danwerner21/we816/Support/images/case8.jpg

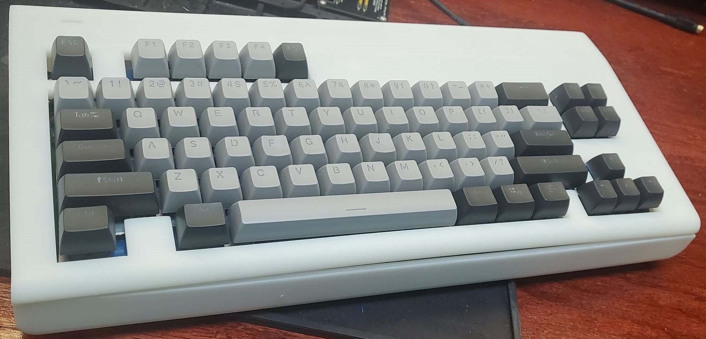
Support/images/case8.jpg
