danwerner21/we816/Support/images/case11.jpg

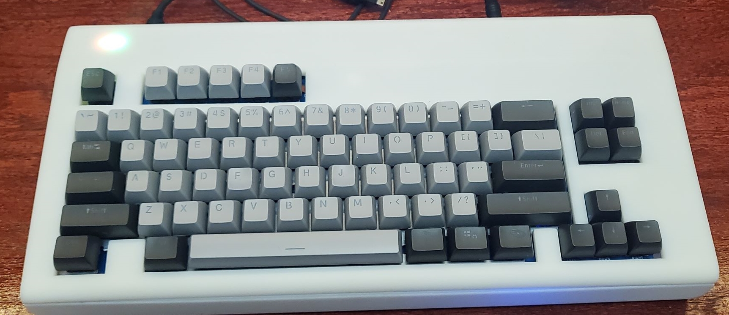
Support/images/case11.jpg
