danwerner21/we816/Support/images/case14.jpg

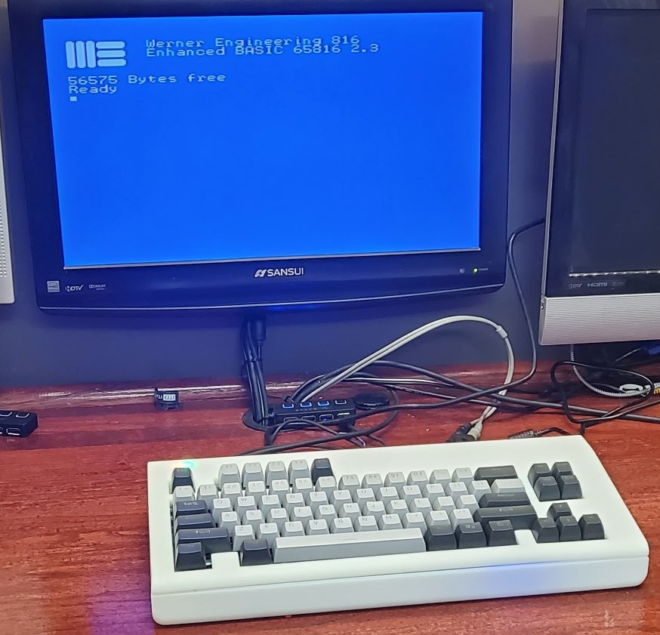
Support/images/case14.jpg
