danwerner21/we816/Support/images/case15.jpg

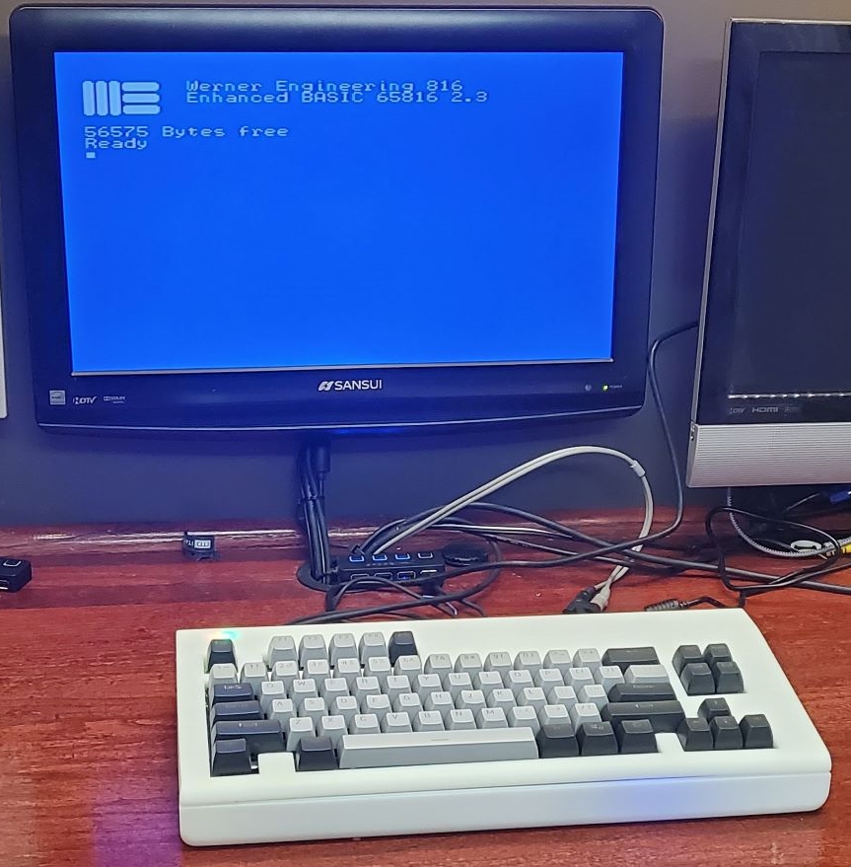
Support/images/case15.jpg
