danwerner21/we816/Hardware/file5FFCADA1.kicad_sch

## KiCad design Hardware/file5FFCADA1.kicad_sch (2022-08-01)

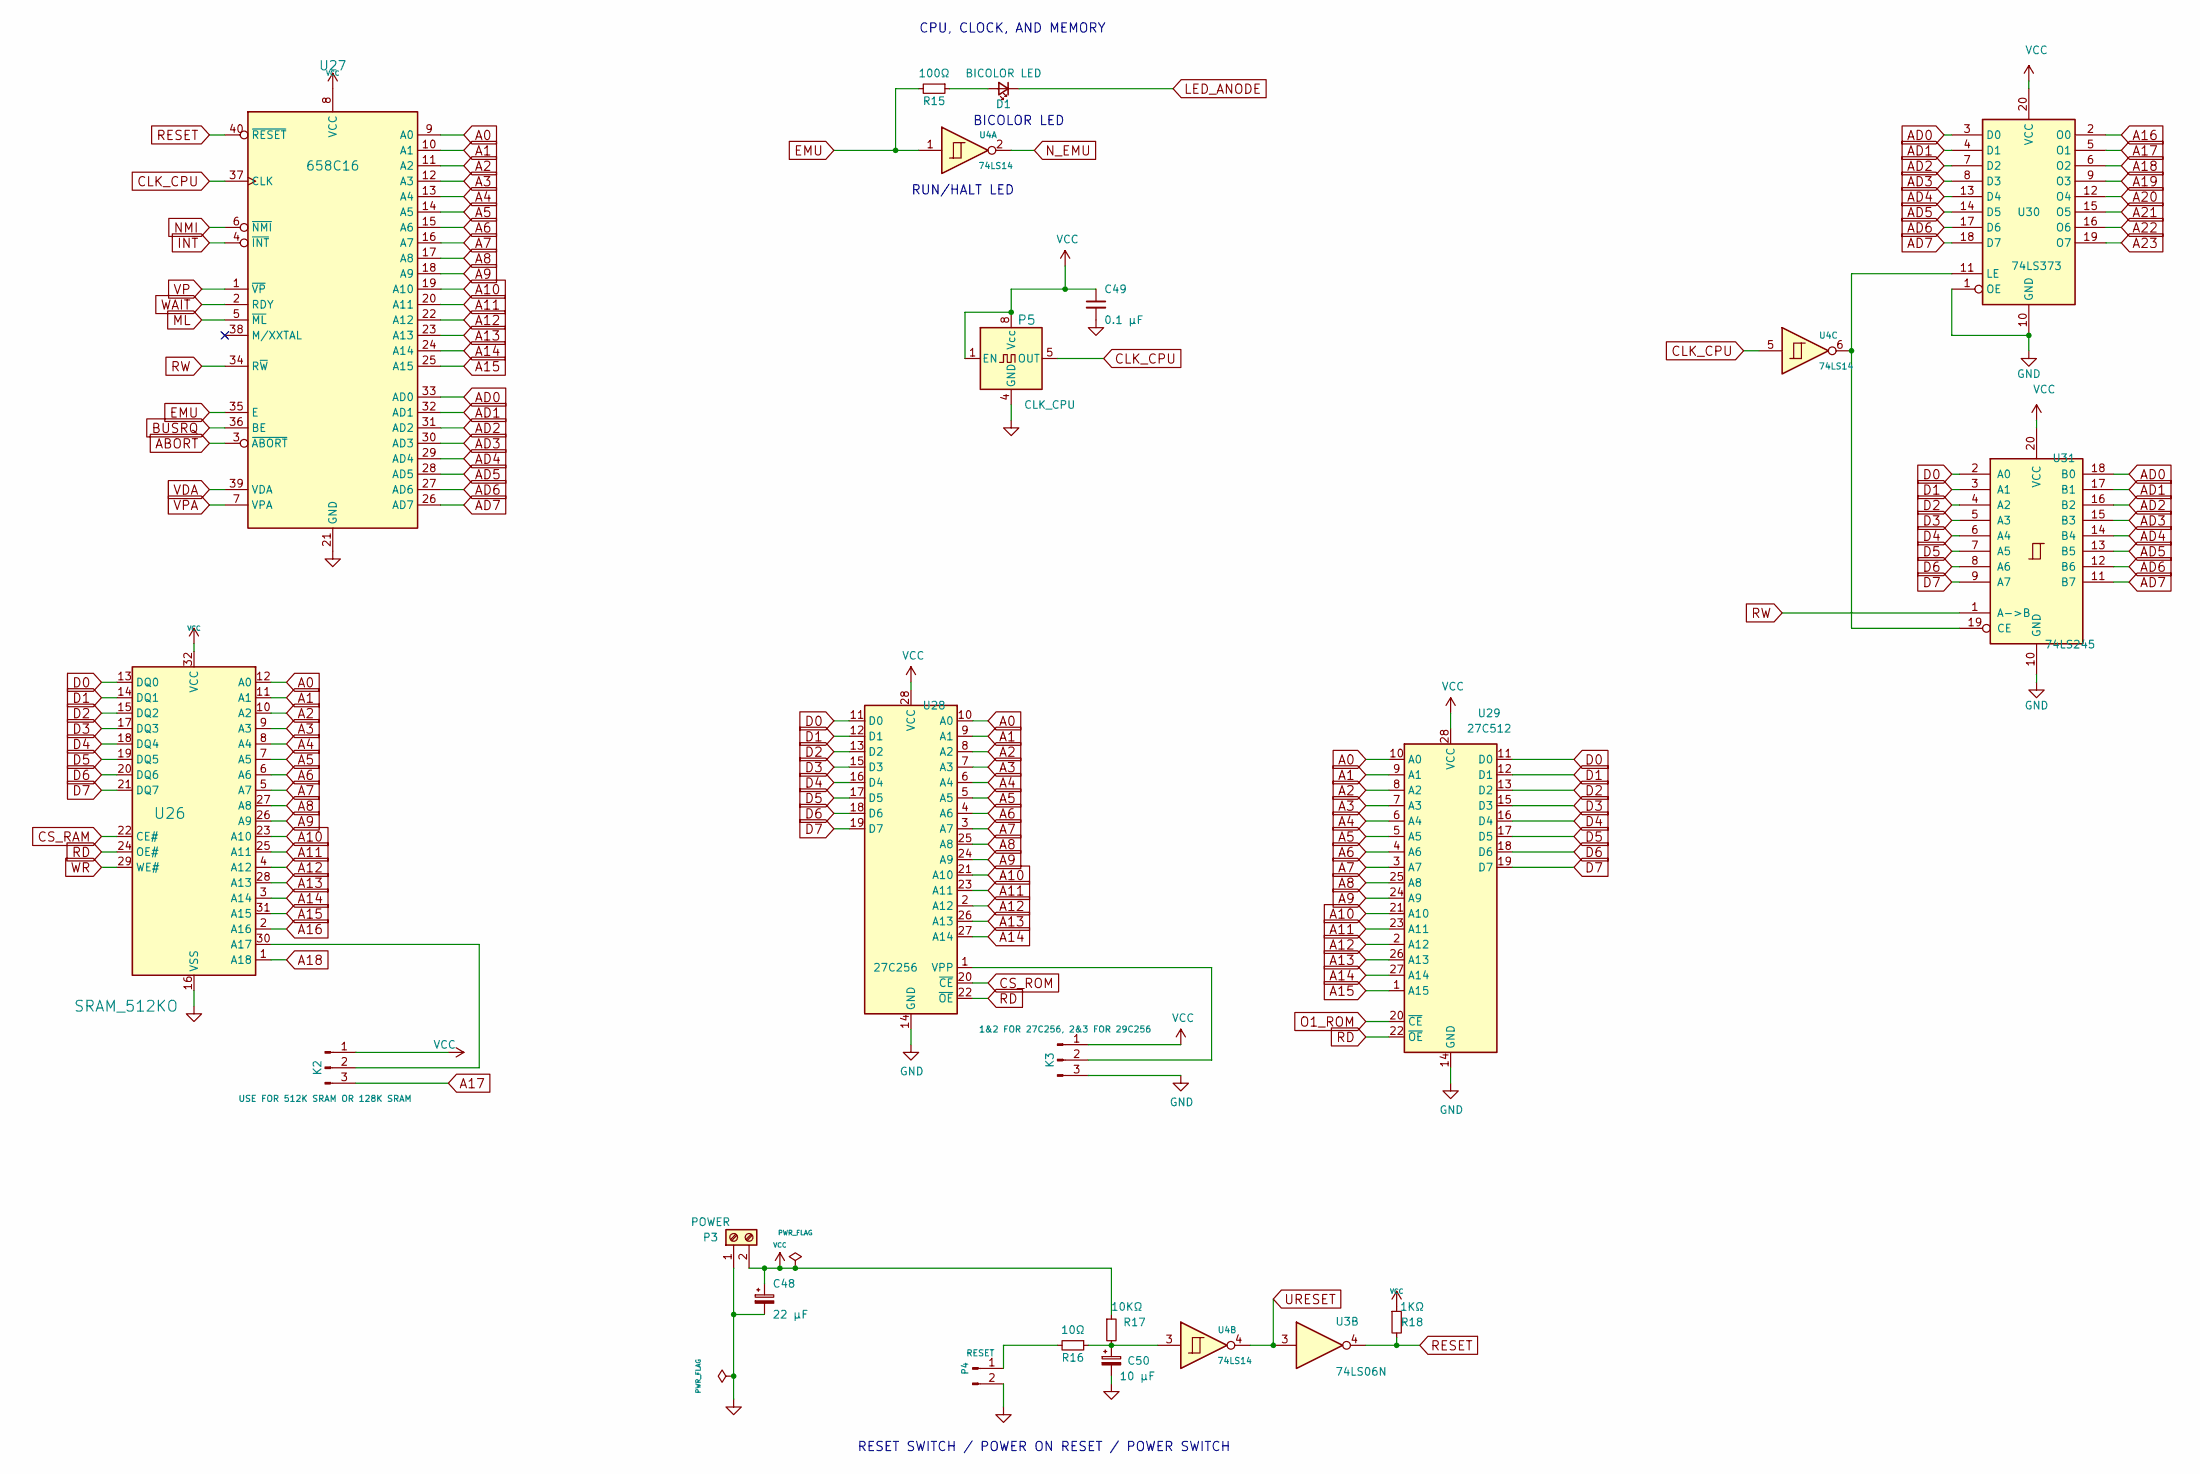
[picture p60: schematic file5FFCADA1.kicad_sch]

Parts:
C48: 22 µF; CP_Radial_D4.0mm_P2.00mm
C49: 0.1 µF; C_Rect_L7.0mm_W2.0mm_P5.00mm
C50: 10 µF; CP_Radial_D4.0mm_P2.00mm
D1: BICOLOR LED; LED_D5.0mm
K2: USE FOR 512K SRAM OR 128K SRAM; PinHeader_1x03_P2.54mm_Vertical
K3: 1&2 FOR 27C256, 2&3 FOR 29C256; PinHeader_1x03_P2.54mm_Vertical
P3: POWER; TerminalBlock_RND_205-00003_1x04_P5.00mm_Horizontal
P4: RESET; PinHeader_1x02_P2.54mm_Vertical
P5: CLK_CPU; Oscillator_DIP-8
R15: 100Ω; R_Axial_DIN0204_L3.6mm_D1.6mm_P5.08mm_Horizontal
R16: 10Ω; R_Axial_DIN0204_L3.6mm_D1.6mm_P5.08mm_Horizontal
R17: 10KΩ; R_Axial_DIN0204_L3.6mm_D1.6mm_P5.08mm_Horizontal
R18: 1KΩ; R_Axial_DIN0204_L3.6mm_D1.6mm_P5.08mm_Horizontal
U3: 74LS06N; DIP-14_W7.62mm_Socket
U4: 74LS14; DIP-14_W7.62mm_Socket_LongPads
U26: SRAM_512KO; DIP-32_W15.24mm
U27: 658C16; DIP-40_W15.24mm_Socket
U28: 27C256; DIP-28_W15.24mm
U29: 27C512; DIP-28_W15.24mm
U30: 74LS373; DIP-20_W7.62mm_Socket_LongPads
U31: 74LS245; DIP-20_W7.62mm_Socket_LongPads

Connections:
A0: U26.12 (A0), U27.9 (A0), U28.10 (A0), U29.10 (A0)
A1: U26.11 (A1), U27.10 (A1), U28.9 (A1), U29.9 (A1)
A2: U26.10 (A2), U27.11 (A2), U28.8 (A2), U29.8 (A2)
A3: U26.9 (A3), U27.12 (A3), U28.7 (A3), U29.7 (A3)
A4: U26.8 (A4), U27.13 (A4), U28.6 (A4), U29.6 (A4)
A5: U26.7 (A5), U27.14 (A5), U28.5 (A5), U29.5 (A5)
A6: U26.6 (A6), U27.15 (A6), U28.4 (A6), U29.4 (A6)
A7: U26.5 (A7), U27.16 (A7), U28.3 (A7), U29.3 (A7)
A8: U26.27 (A8), U27.17 (A8), U28.25 (A8), U29.25 (A8)
A9: U26.26 (A9), U27.18 (A9), U28.24 (A9), U29.24 (A9)
A10: U26.23 (A10), U27.19 (A10), U28.21 (A10), U29.21 (A10)
A11: U26.25 (A11), U27.20 (A11), U28.23 (A11), U29.23 (A11)
A12: U26.4 (A12), U27.22 (A12), U28.2 (A12), U29.2 (A12)
A13: U26.28 (A13), U27.23 (A13), U28.26 (A13), U29.26 (A13)
A14: U26.3 (A14), U27.24 (A14), U28.27 (A14), U29.27 (A14)
A15: U26.31 (A15), U27.25 (A15), U29.1 (A15)
A16: U26.2 (A16), U30.2 (O0)
A17: K2.3, U30.5 (O1)
A18: U26.1 (A18), U30.6 (O2)
A19: U30.9 (O3)
A20: U30.12 (O4)
A21: U30.15 (O5)
A22: U30.16 (O6)
A23: U30.19 (O7)
ABORT: U27.3 (~ABORT)
AD0: U27.33 (AD0), U30.3 (D0), U31.18 (B0)
AD1: U27.32 (AD1), U30.4 (D1), U31.17 (B1)
AD2: U27.31 (AD2), U30.7 (D2), U31.16 (B2)
AD3: U27.30 (AD3), U30.8 (D3), U31.15 (B3)
AD4: U27.29 (AD4), U30.13 (D4), U31.14 (B4)
AD5: U27.28 (AD5), U30.14 (D5), U31.13 (B5)
AD6: U27.27 (AD6), U30.17 (D6), U31.12 (B6)
AD7: U27.26 (AD7), U30.18 (D7), U31.11 (B7)
BUSRQ: U27.36 (BE)
CLK_CPU: P5.5 (OUT), U4.5, U27.37 (CLK)
CS_RAM: U26.22 (CE#)
CS_ROM: U28.20 (~CE)
D0: U26.13 (DQ0), U28.11 (D0), U29.11 (D0), U31.2 (A0)
D1: U26.14 (DQ1), U28.12 (D1), U29.12 (D1), U31.3 (A1)
D2: U26.15 (DQ2), U28.13 (D2), U29.13 (D2), U31.4 (A2)
D3: U26.17 (DQ3), U28.15 (D3), U29.15 (D3), U31.5 (A3)
D4: U26.18 (DQ4), U28.16 (D4), U29.16 (D4), U31.6 (A4)
D5: U26.19 (DQ5), U28.17 (D5), U29.17 (D5), U31.7 (A5)
D6: U26.20 (DQ6), U28.18 (D6), U29.18 (D6), U31.8 (A6)
D7: U26.21 (DQ7), U28.19 (D7), U29.19 (D7), U31.9 (A7)
EMU: R15.2, U4.1, U27.35 (E)
GND: C48.2, C49.2, C50.2, K3.3, P3.1, P4.2, P5.4 (GND), U26.16 (VSS), U27.21 (GND), U28.14 (GND), U29.14 (GND), U30.1 (OE), U30.10 (GND), U31.10 (GND)
INT: U27.4 (~INT)
LED_ANODE: D1.1 (K)
ML: U27.5 (~ML)
NMI: U27.6 (~NMI)
N_EMU: U4.2
unnamed: C50.1, R16.1, R17.2, U4.3
unnamed: D1.2 (A), R15.1
unnamed: K2.2, U26.30 (A17)
unnamed: K3.2, U28.1 (VPP)
unnamed: P4.1, R16.2
unnamed: U4.6, U30.11 (LE), U31.19 (CE)
O1_ROM: U29.20 (~CE)
RD: U26.24 (OE#), U28.22 (~OE), U29.22 (~OE)
RESET: R18.2, U3.4, U27.40 (~RESET)
RW: U27.34 (R~W), U31.1 (A->B)
URESET: U3.3, U4.4
VCC: C48.1, C49.1, K2.1, K3.1, P3.2, P5.1 (EN), P5.8 (Vcc), R17.1, R18.1, U26.32 (VCC), U27.8 (VCC), U28.28 (VCC), U29.28 (VCC), U30.20 (VCC), U31.20 (VCC)
VDA: U27.39 (VDA)
VP: U27.1 (~VP)
VPA: U27.7 (VPA)
WAIT: U27.2 (RDY)
WR: U26.29 (WE#)

Notes on the sheet:
RUN/HALT LED
CPU, CLOCK, AND MEMORY
RESET SWITCH / POWER ON RESET / POWER SWITCH
BICOLOR LED
