danwerner21/we816/Hardware/file5FFCBF10.kicad_sch

## KiCad design Hardware/file5FFCBF10.kicad_sch (2022-08-01)

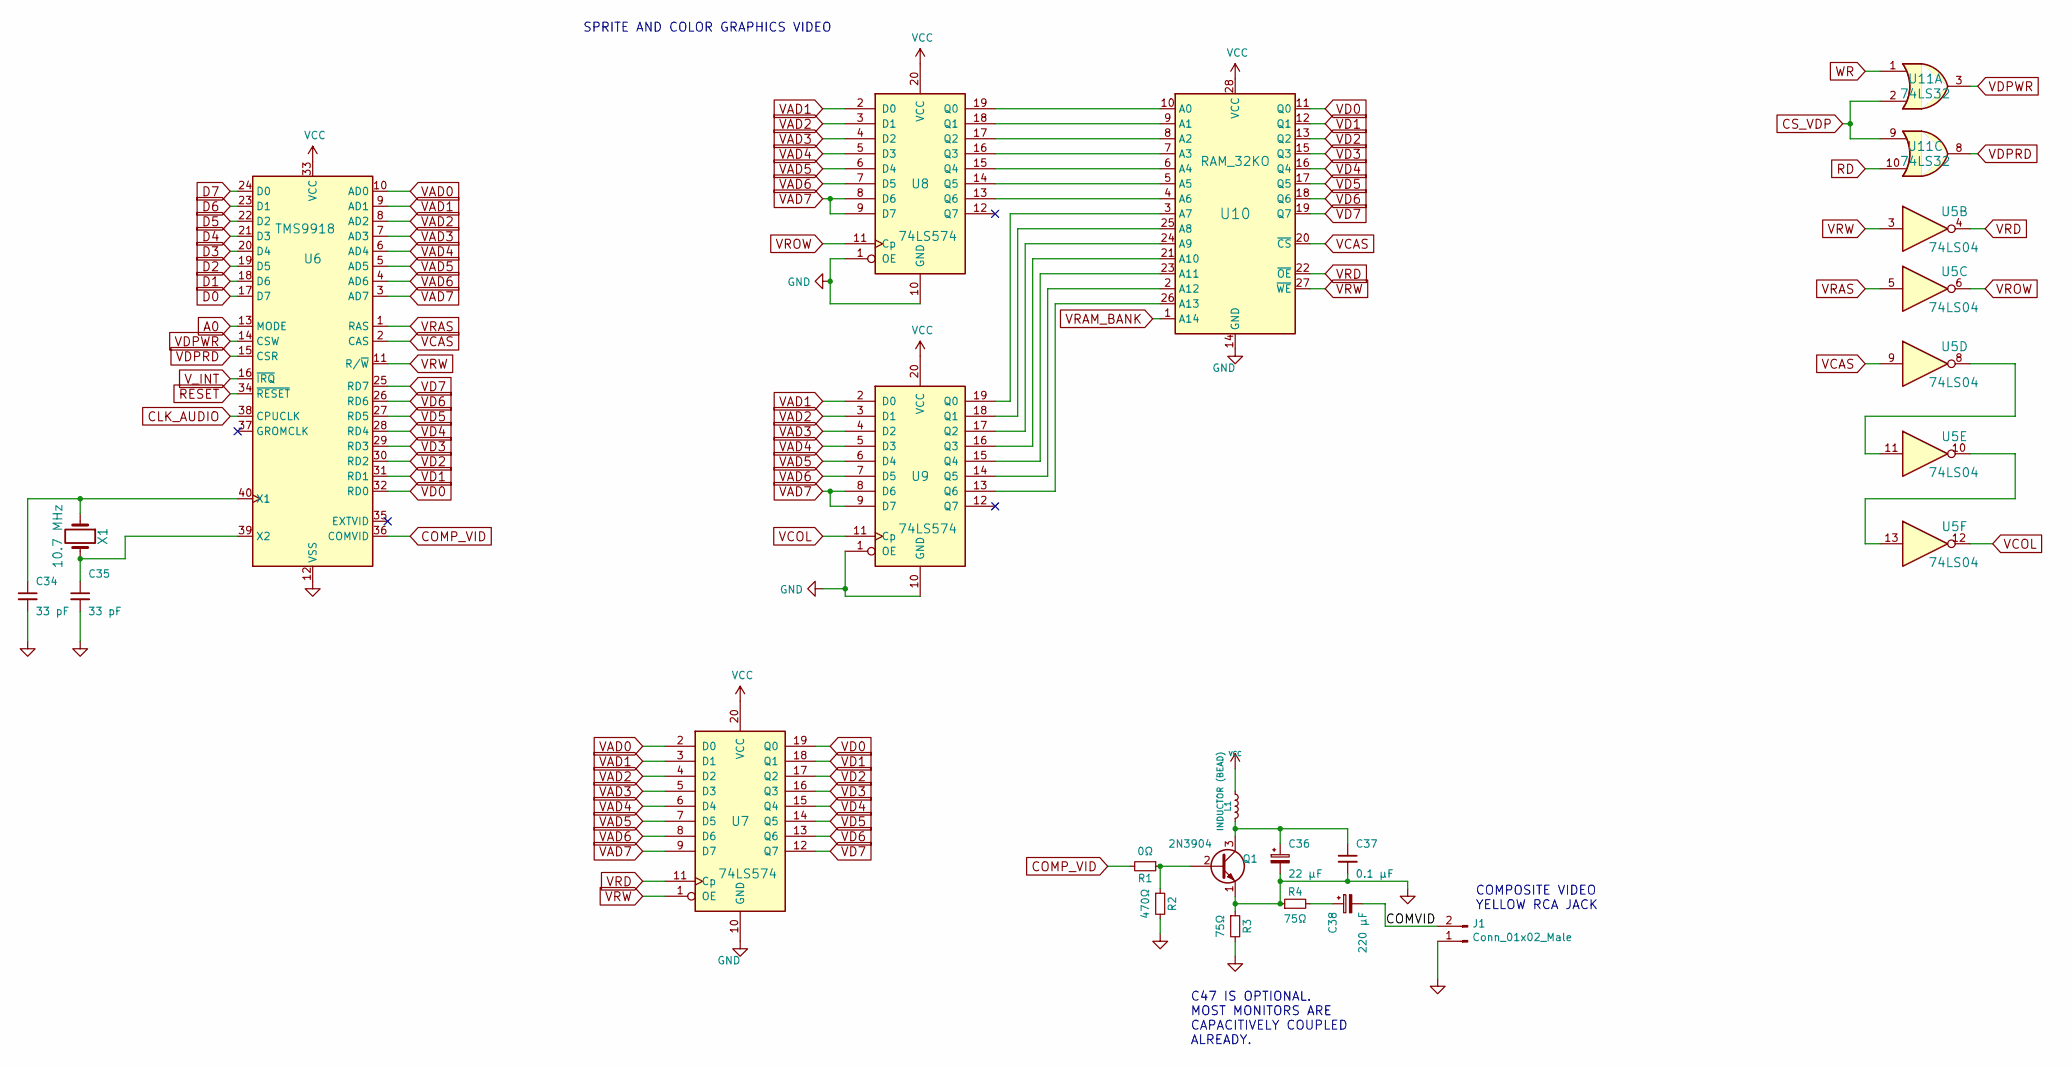
[picture p61: schematic file5FFCBF10.kicad_sch]

Parts:
C34, C35: 33 pF; C_Rect_L7.0mm_W2.0mm_P5.00mm
C36: 22 µF; CP_Radial_D4.0mm_P2.00mm
C37: 0.1 µF; C_Rect_L7.0mm_W2.0mm_P5.00mm
C38: 220 µF; CP_Radial_D4.0mm_P2.00mm
J1: Conn_01x02_Male; CUI_RCJ-041
L1: INDUCTOR (BEAD); R_Axial_DIN0207_L6.3mm_D2.5mm_P10.16mm_Horizontal
Q1: 2N3904; TO-92L_HandSolder
R1: 0Ω; R_Axial_DIN0204_L3.6mm_D1.6mm_P5.08mm_Horizontal
R2: 470Ω; R_Axial_DIN0204_L3.6mm_D1.6mm_P5.08mm_Horizontal
R3, R4: 75Ω; R_Axial_DIN0204_L3.6mm_D1.6mm_P5.08mm_Horizontal
U5: 74LS04; DIP-14_W7.62mm_Socket
U6: TMS9918; DIP-40_W15.24mm_Socket_LongPads
U7: 74LS574; DIP-20_W7.62mm_Socket
U8, U9: 74LS574; DIP-20_W7.62mm_Socket_LongPads
U10: RAM_32KO; DIP-28_W15.24mm
U11: 74LS32; DIP-14_W7.62mm_Socket
X1: 10.7 MHz; Crystal_HC18-U_Vertical

Connections:
A0: U6.13 (MODE)
CLK_AUDIO: U6.38 (CPUCLK)
COMP_VID: R1.2, U6.36 (COMVID)
COMVID: C38.2, J1.2
CS_VDP: U11.2, U11.9
D0: U6.17 (D7)
D1: U6.18 (D6)
D2: U6.19 (D5)
D3: U6.20 (D4)
D4: U6.21 (D3)
D5: U6.22 (D2)
D6: U6.23 (D1)
D7: U6.24 (D0)
GND: C34.2, C35.2, C36.2, C37.2, J1.1, Q1.1 (E), R2.2, R3.1, R3.2, R4.1, U6.12 (VSS), U7.10 (GND), U8.1 (OE), U8.10 (GND), U9.1 (OE), U9.10 (GND), U10.14 (GND)
unnamed: C34.1, U6.40 (X1), X1.1
unnamed: C35.1, U6.39 (X2), X1.2
unnamed: C36.1, C37.1, L1.2, Q1.3 (C)
unnamed: C38.1, R4.2
unnamed: Q1.2 (B), R1.1, R2.1
unnamed: U5.10, U5.13
unnamed: U5.8, U5.11
unnamed: U9.14 (Q5), U10.2 (A12)
unnamed: U9.19 (Q0), U10.3 (A7)
unnamed: U8.13 (Q6), U10.4 (A6)
unnamed: U8.14 (Q5), U10.5 (A5)
unnamed: U8.15 (Q4), U10.6 (A4)
unnamed: U8.16 (Q3), U10.7 (A3)
unnamed: U8.17 (Q2), U10.8 (A2)
unnamed: U8.18 (Q1), U10.9 (A1)
unnamed: U8.19 (Q0), U10.10 (A0)
unnamed: U9.16 (Q3), U10.21 (A10)
unnamed: U9.15 (Q4), U10.23 (A11)
unnamed: U9.17 (Q2), U10.24 (A9)
unnamed: U9.18 (Q1), U10.25 (A8)
unnamed: U9.13 (Q6), U10.26 (A13)
RD: U11.10
RESET: U6.34 (~RESET)
VAD0: U6.10 (AD0), U7.2 (D0)
VAD1: U6.9 (AD1), U7.3 (D1), U8.2 (D0), U9.2 (D0)
VAD2: U6.8 (AD2), U7.4 (D2), U8.3 (D1), U9.3 (D1)
VAD3: U6.7 (AD3), U7.5 (D3), U8.4 (D2), U9.4 (D2)
VAD4: U6.6 (AD4), U7.6 (D4), U8.5 (D3), U9.5 (D3)
VAD5: U6.5 (AD5), U7.7 (D5), U8.6 (D4), U9.6 (D4)
VAD6: U6.4 (AD6), U7.8 (D6), U8.7 (D5), U9.7 (D5)
VAD7: U6.3 (AD7), U7.9 (D7), U8.8 (D6), U8.9 (D7), U9.8 (D6), U9.9 (D7)
VCAS: U5.9, U6.2 (CAS), U10.20 (~CS)
VCC: L1.1, U6.33 (VCC), U7.20 (VCC), U8.20 (VCC), U9.20 (VCC), U10.28 (VCC)
VCOL: U5.12, U9.11 (Cp)
VD0: U6.32 (RD0), U7.19 (Q0), U10.11 (Q0)
VD1: U6.31 (RD1), U7.18 (Q1), U10.12 (Q1)
VD2: U6.30 (RD2), U7.17 (Q2), U10.13 (Q2)
VD3: U6.29 (RD3), U7.16 (Q3), U10.15 (Q3)
VD4: U6.28 (RD4), U7.15 (Q4), U10.16 (Q4)
VD5: U6.27 (RD5), U7.14 (Q5), U10.17 (Q5)
VD6: U6.26 (RD6), U7.13 (Q6), U10.18 (Q6)
VD7: U6.25 (RD7), U7.12 (Q7), U10.19 (Q7)
VDPRD: U6.15 (CSR), U11.8
VDPWR: U6.14 (CSW), U11.3
VRAM_BANK: U10.1 (A14)
VRAS: U5.5, U6.1 (RAS)
VRD: U5.4, U7.11 (Cp), U10.22 (~OE)
VROW: U5.6, U8.11 (Cp)
VRW: U5.3, U6.11 (R/~W), U7.1 (OE), U10.27 (~WE)
V_INT: U6.16 (~IRQ)
WR: U11.1

Notes on the sheet:
SPRITE AND COLOR GRAPHICS VIDEO
COMPOSITE VIDEO YELLOW RCA JACK
C47 IS OPTIONAL. MOST MONITORS ARE CAPACITIVELY COUPLED ALREADY.
