danwerner21/we816/Hardware/file5FFCD08B.kicad_sch

## KiCad design Hardware/file5FFCD08B.kicad_sch (2022-08-01)

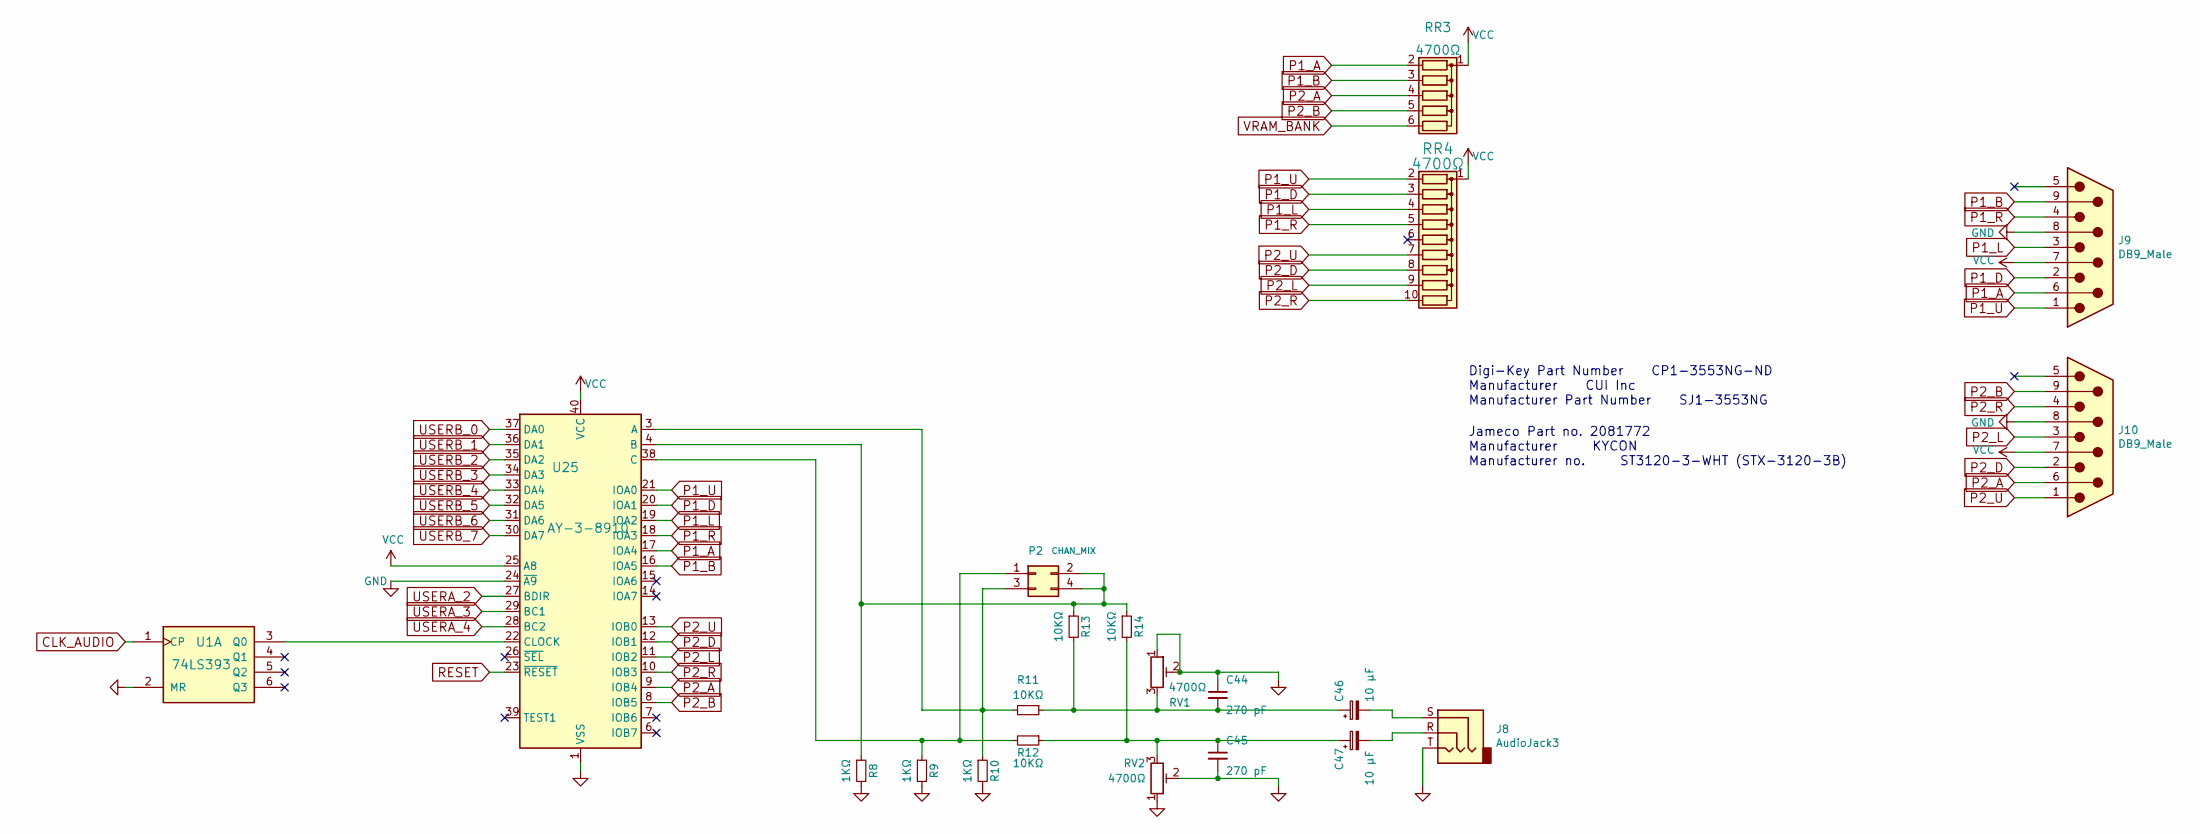
[picture p62: schematic file5FFCD08B.kicad_sch]

Parts:
C44, C45: 270 pF; C_Rect_L7.0mm_W2.0mm_P5.00mm
C46, C47: 10 µF; CP_Radial_D4.0mm_P2.00mm
J8: AudioJack3; Jack_3.5mm_CUI_SJ1-3533NG_Horizontal_CircularHoles
J9, J10: DB9_Male; DSUB-9_Male_Horizontal_P2.77x2.84mm_EdgePinOffset9.90mm_Hou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
P2: CHAN_MIX; PinHeader_2x02_P2.54mm_Vertical
R8, R9, R10: 1KΩ; R_Axial_DIN0204_L3.6mm_D1.6mm_P5.08mm_Horizontal
R11, R12, R13, R14: 10KΩ; R_Axial_DIN0204_L3.6mm_D1.6mm_P5.08mm_Horizontal
RR3: 4700Ω; R_Array_SIP6
RR4: 4700Ω; R_Array_SIP10
RV1, RV2: 4700Ω; Potentiometer_ACP_CA9-V10_Vertical
U1: 74LS393; DIP-14_W7.62mm_Socket
U25: AY-3-8910; DIP-40_W15.24mm

Connections:
CLK_AUDIO: U1.1 (CP)
GND: C44.1, C45.2, J8.T, J9.8, J10.8, R8.2, R9.2, R10.2, RV1.1, RV1.2, RV2.1, RV2.2, U1.2 (MR), U25.1 (VSS), U25.24 (~A9)
unnamed: C44.2, C46.1, R11.1, R13.2, RV1.3
unnamed: C45.1, C47.1, R12.1, R14.2, RV2.3
unnamed: C46.2, J8.S
unnamed: C47.2, J8.R
unnamed: P2.1, R9.1, R12.2, U25.38 (C)
unnamed: P2.2, P2.4, R8.1, R13.1, R14.1, U25.4 (B)
unnamed: P2.3, R10.1, R11.2, U25.3 (A)
unnamed: U1.3 (Q0), U25.22 (CLOCK)
P1_A: J9.6, RR3.2 (R1), U25.17 (IOA4)
P1_B: J9.9, RR3.3 (R2), U25.16 (IOA5)
P1_D: J9.2, RR4.3 (R2), U25.20 (IOA1)
P1_L: J9.3, RR4.4 (R3), U25.19 (IOA2)
P1_R: J9.4, RR4.5 (R4), U25.18 (IOA3)
P1_U: J9.1, RR4.2 (R1), U25.21 (IOA0)
P2_A: J10.6, RR3.4 (R3), U25.9 (IOB4)
P2_B: J10.9, RR3.5 (R4), U25.8 (IOB5)
P2_D: J10.2, RR4.8 (R7), U25.12 (IOB1)
P2_L: J10.3, RR4.9 (R8), U25.11 (IOB2)
P2_R: J10.4, RR4.10 (R9), U25.10 (IOB3)
P2_U: J10.1, RR4.7 (R6), U25.13 (IOB0)
RESET: U25.23 (~RESET)
USERA_2: U25.27 (BDIR)
USERA_3: U25.29 (BC1)
USERA_4: U25.28 (BC2)
USERB_0: U25.37 (DA0)
USERB_1: U25.36 (DA1)
USERB_2: U25.35 (DA2)
USERB_3: U25.34 (DA3)
USERB_4: U25.33 (DA4)
USERB_5: U25.32 (DA5)
USERB_6: U25.31 (DA6)
USERB_7: U25.30 (DA7)
VCC: J9.7, J10.7, RR3.1 (common), RR4.1 (common), U25.25 (A8), U25.40 (VCC)
VRAM_BANK: RR3.6 (R5)

Notes on the sheet:
Digi-Key Part Number CP1-3553NG-ND Manufacturer CUI Inc Manufacturer Part Number SJ1-3553NG
Jameco Part no. 2081772 Manufacturer KYCON Manufacturer no. ST3120-3-WHT (STX-3120-3B)
