danwerner21/we816/Hardware/file5FFCE1F7.kicad_sch

## KiCad design Hardware/file5FFCE1F7.kicad_sch (2022-08-01)

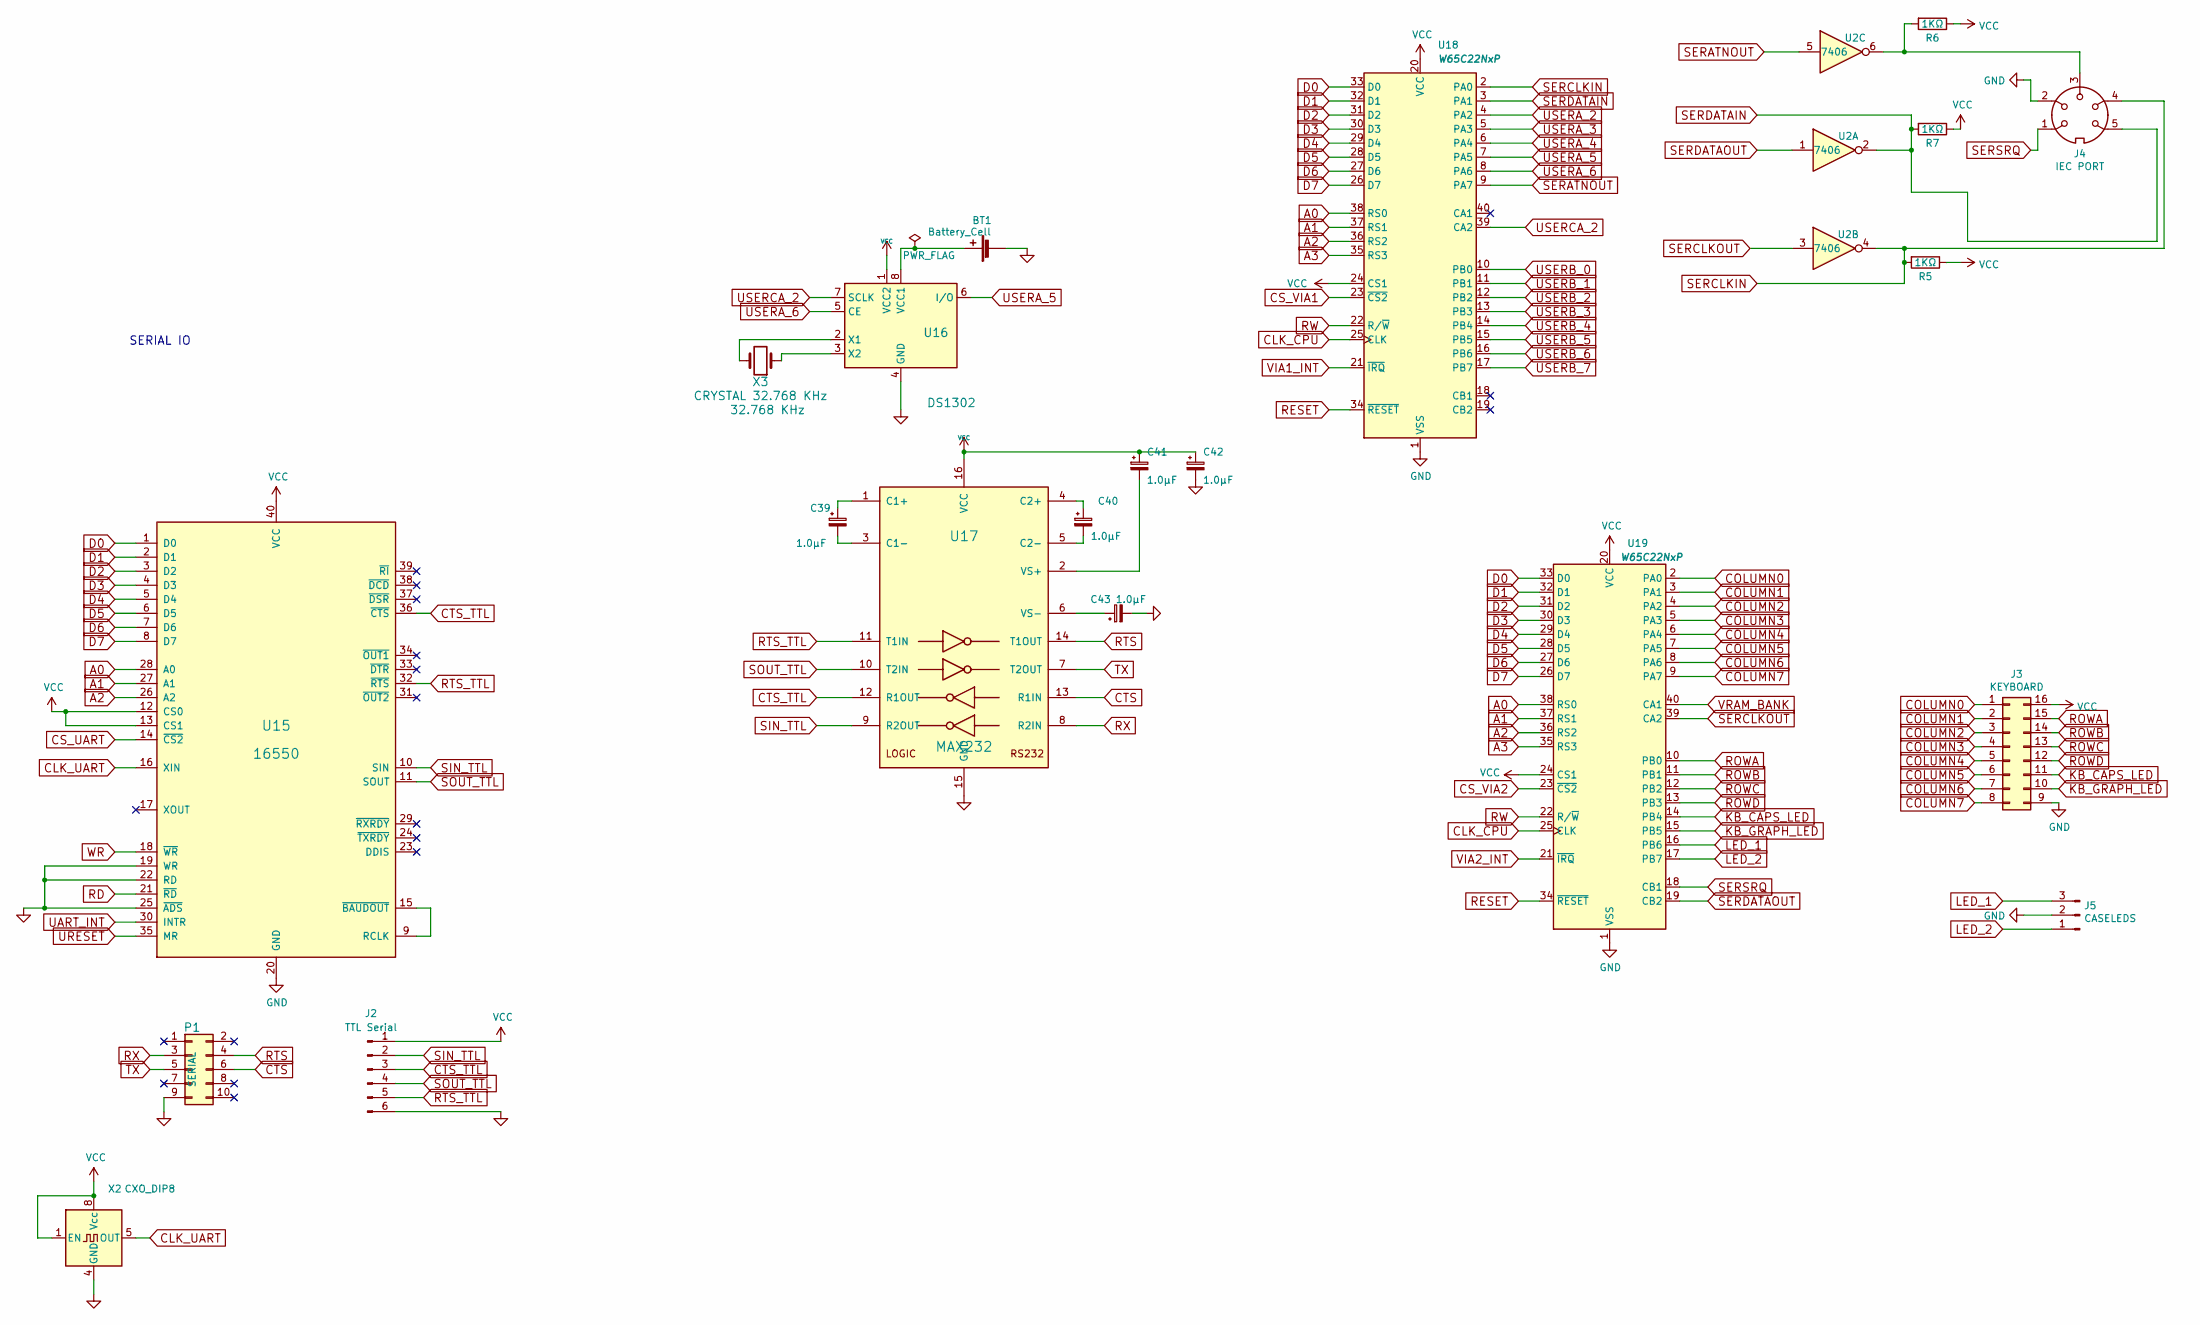
[picture p63: schematic file5FFCE1F7.kicad_sch]

Parts:
BT1: Battery_Cell; Battery_Holder_Coin_2032_BS-7_FIXED
C39, C40, C41, C42, C43: 1.0µF; CP_Radial_D4.0mm_P2.00mm
J2: TTL Serial; PinHeader_1x06_P2.54mm_Vertical
J3: KEYBOARD; PinHeader_2x08_P2.54mm_Vertical
J4: IEC PORT; din6
J5: CASELEDS; PinHeader_1x03_P2.54mm_Vertical
P1: SERIAL; PinHeader_2x05_P2.54mm_Vertical
R5, R6, R7: 1KΩ; R_Axial_DIN0204_L3.6mm_D1.6mm_P5.08mm_Horizontal
U2: 7406; DIP-14_W7.62mm_Socket
U15: 16550; DIP-40_W15.24mm
U16: DS1302; DIP-8_W7.62mm
U17: MAX232; DIP-16_W7.62mm_Socket_LongPads
U18, U19: W65C22NxP; DIP-40_W15.24mm_Socket
X2: CXO_DIP8; Oscillator_DIP-8
X3: CRYSTAL 32.768 KHz; Crystal_Round_D1.5mm_Vertical

Connections:
A0: U15.28 (A0), U18.38 (RS0), U19.38 (RS0)
A1: U15.27 (A1), U18.37 (RS1), U19.37 (RS1)
A2: U15.26 (A2), U18.36 (RS2), U19.36 (RS2)
A3: U18.35 (RS3), U19.35 (RS3)
CLK_CPU: U18.25 (CLK), U19.25 (CLK)
CLK_UART: U15.16 (XIN), X2.5 (OUT)
COLUMN0: J3.1, U19.2 (PA0)
COLUMN1: J3.2, U19.3 (PA1)
COLUMN2: J3.3, U19.4 (PA2)
COLUMN3: J3.4, U19.5 (PA3)
COLUMN4: J3.5, U19.6 (PA4)
COLUMN5: J3.6, U19.7 (PA5)
COLUMN6: J3.7, U19.8 (PA6)
COLUMN7: J3.8, U19.9 (PA7)
CS_UART: U15.14 (~CS2)
CS_VIA1: U18.23 (~CS2)
CS_VIA2: U19.23 (~CS2)
CTS: P1.6, U17.13 (R1IN)
CTS_TTL: J2.3, U15.36 (~CTS), U17.12 (R1OUT)
D0: U15.1 (D0), U18.33 (D0), U19.33 (D0)
D1: U15.2 (D1), U18.32 (D1), U19.32 (D1)
D2: U15.3 (D2), U18.31 (D2), U19.31 (D2)
D3: U15.4 (D3), U18.30 (D3), U19.30 (D3)
D4: U15.5 (D4), U18.29 (D4), U19.29 (D4)
D5: U15.6 (D5), U18.28 (D5), U19.28 (D5)
D6: U15.7 (D6), U18.27 (D6), U19.27 (D6)
D7: U15.8 (D7), U18.26 (D7), U19.26 (D7)
GND: BT1.2 (-), C42.2, C43.2, J2.6, J3.9, J4.2, J5.2, P1.9, U15.19 (WR), U15.20 (GND), U15.22 (RD), U15.25 (~ADS), U16.4 (GND), U17.15 (GND), U18.1 (VSS), U19.1 (VSS), X2.4 (GND)
KB_CAPS_LED: J3.11, U19.14 (PB4)
KB_GRAPH_LED: J3.10, U19.15 (PB5)
LED_1: J5.3, U19.16 (PB6)
LED_2: J5.1, U19.17 (PB7)
unnamed: BT1.1 (+), U16.8 (VCC1)
unnamed: C39.1, U17.1 (C1+)
unnamed: C39.2, U17.3 (C1-)
unnamed: C40.1, U17.4 (C2+)
unnamed: C40.2, U17.5 (C2-)
unnamed: C41.2, U17.2 (VS+)
unnamed: C43.1, U17.6 (VS-)
unnamed: J4.3, R6.2, U2.6
unnamed: U15.9 (RCLK), U15.15 (~BAUDOUT)
unnamed: U16.2 (X1), X3.2
unnamed: U16.3 (X2), X3.1
RD: U15.21 (~RD)
RESET: U18.34 (~RESET), U19.34 (~RESET)
ROWA: J3.15, U19.10 (PB0)
ROWB: J3.14, U19.11 (PB1)
ROWC: J3.13, U19.12 (PB2)
ROWD: J3.12, U19.13 (PB3)
RTS: P1.4, U17.14 (T1OUT)
RTS_TTL: J2.5, U15.32 (~RTS), U17.11 (T1IN)
RW: U18.22 (R/~W), U19.22 (R/~W)
RX: P1.3, U17.8 (R2IN)
SERATNOUT: U2.5, U18.9 (PA7)
SERCLKIN: J4.4, R5.2, U2.4, U18.2 (PA0)
SERCLKOUT: U2.3, U19.39 (CA2)
SERDATAIN: J4.5, R7.2, U2.2, U18.3 (PA1)
SERDATAOUT: U2.1, U19.19 (CB2)
SERSRQ: J4.1, U19.18 (CB1)
SIN_TTL: J2.2, U15.10 (SIN), U17.9 (R2OUT)
SOUT_TTL: J2.4, U15.11 (SOUT), U17.10 (T2IN)
TX: P1.5, U17.7 (T2OUT)
UART_INT: U15.30 (INTR)
URESET: U15.35 (MR)
USERA_2: U18.4 (PA2)
USERA_3: U18.5 (PA3)
USERA_4: U18.6 (PA4)
USERA_5: U16.6 (I/O), U18.7 (PA5)
USERA_6: U16.5 (CE), U18.8 (PA6)
USERB_0: U18.10 (PB0)
USERB_1: U18.11 (PB1)
USERB_2: U18.12 (PB2)
USERB_3: U18.13 (PB3)
USERB_4: U18.14 (PB4)
USERB_5: U18.15 (PB5)
USERB_6: U18.16 (PB6)
USERB_7: U18.17 (PB7)
USERCA_2: U16.7 (SCLK), U18.39 (CA2)
VCC: C41.1, C42.1, J2.1, J3.16, R5.1, R6.1, R7.1, U15.12 (CS0), U15.13 (CS1), U15.40 (VCC), U16.1 (VCC2), U17.16 (VCC), U18.20 (VCC), U18.24 (CS1), U19.20 (VCC), U19.24 (CS1), X2.1 (EN), X2.8 (Vcc)
VIA1_INT: U18.21 (~IRQ)
VIA2_INT: U19.21 (~IRQ)
VRAM_BANK: U19.40 (CA1)
WR: U15.18 (~WR)

Notes on the sheet:
SERIAL IO
