danwerner21/we816/Hardware/file60340596.kicad_sch

## KiCad design Hardware/file60340596.kicad_sch (2022-08-01)

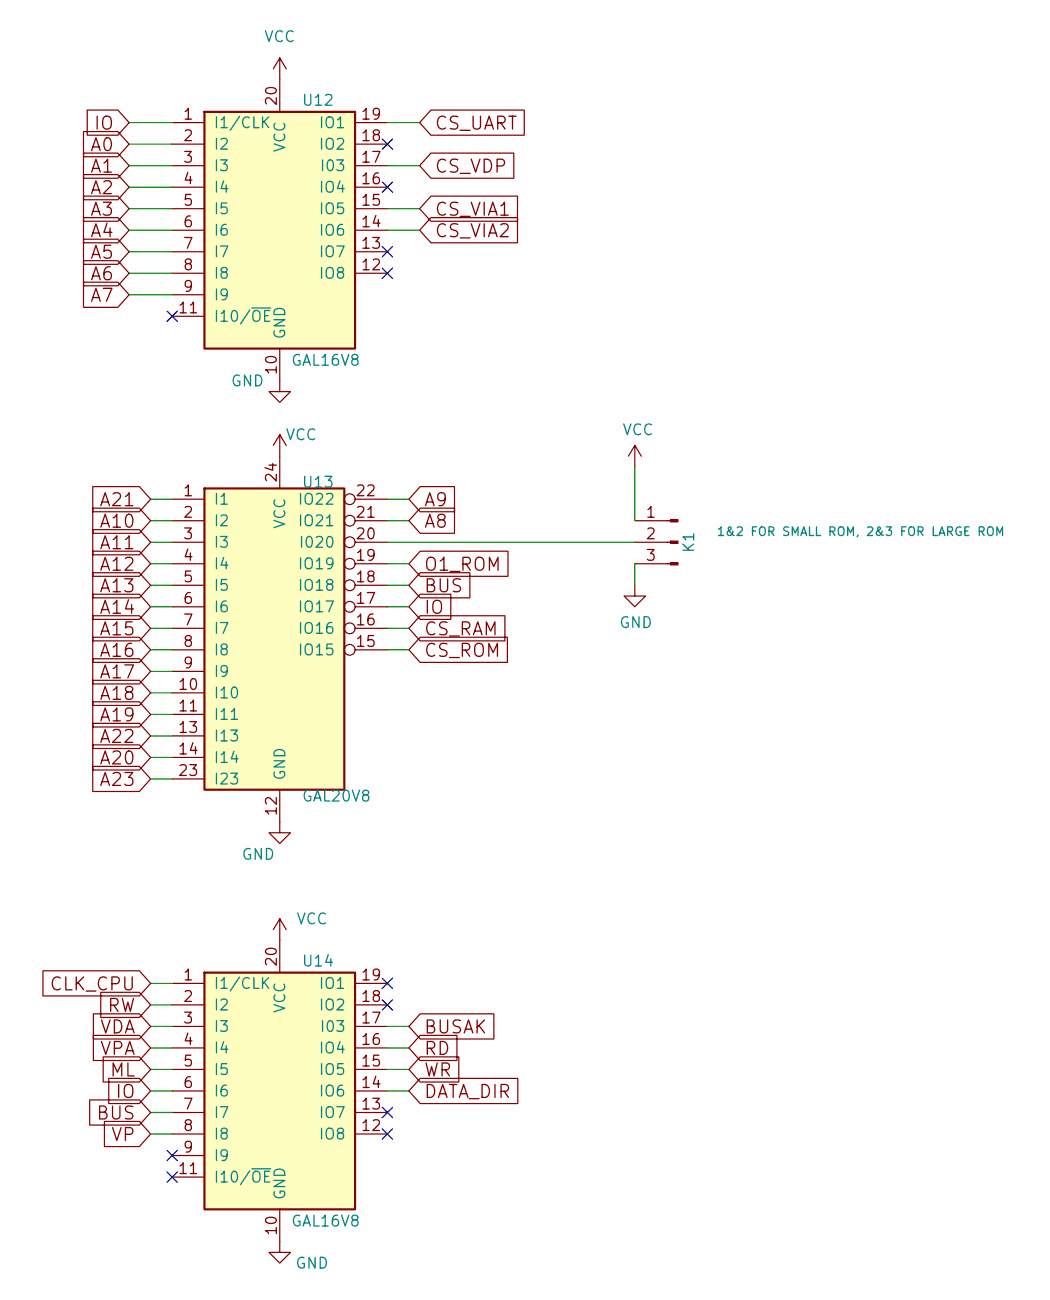
[picture p64: schematic file60340596.kicad_sch]

Parts:
K1: 1&2 FOR SMALL ROM, 2&3 FOR LARGE ROM; PinHeader_1x03_P2.54mm_Vertical
U12, U14: GAL16V8; DIP-20_W7.62mm_Socket_LongPads
U13: GAL20V8; DIP-24_W7.62mm_Socket_LongPads

Connections:
A0: U12.2 (I2)
A1: U12.3 (I3)
A2: U12.4 (I4)
A3: U12.5 (I5)
A4: U12.6 (I6)
A5: U12.7 (I7)
A6: U12.8 (I8)
A7: U12.9 (I9)
A8: U13.21 (IO21)
A9: U13.22 (IO22)
A10: U13.2 (I2)
A11: U13.3 (I3)
A12: U13.4 (I4)
A13: U13.5 (I5)
A14: U13.6 (I6)
A15: U13.7 (I7)
A16: U13.8 (I8)
A17: U13.9 (I9)
A18: U13.10 (I10)
A19: U13.11 (I11)
A20: U13.14 (I14)
A21: U13.1 (I1)
A22: U13.13 (I13)
A23: U13.23 (I23)
BUS: U13.18 (IO18), U14.7 (I7)
BUSAK: U14.17 (I03)
CLK_CPU: U14.1 (I1/CLK)
CS_RAM: U13.16 (IO16)
CS_ROM: U13.15 (IO15)
CS_UART: U12.19 (IO1)
CS_VDP: U12.17 (I03)
CS_VIA1: U12.15 (IO5)
CS_VIA2: U12.14 (IO6)
DATA_DIR: U14.14 (IO6)
GND: K1.3, U12.10 (GND), U13.12 (GND), U14.10 (GND)
IO: U12.1 (I1/CLK), U13.17 (IO17), U14.6 (I6)
ML: U14.5 (I5)
unnamed: K1.2, U13.20 (I020)
O1_ROM: U13.19 (IO19)
RD: U14.16 (IO4)
RW: U14.2 (I2)
VCC: K1.1, U12.20 (VCC), U13.24 (VCC), U14.20 (VCC)
VDA: U14.3 (I3)
VP: U14.8 (I8)
VPA: U14.4 (I4)
WR: U14.15 (IO5)
