danwerner21/we816/Hardware/file60341279.kicad_sch

## KiCad design Hardware/file60341279.kicad_sch (2022-08-01)

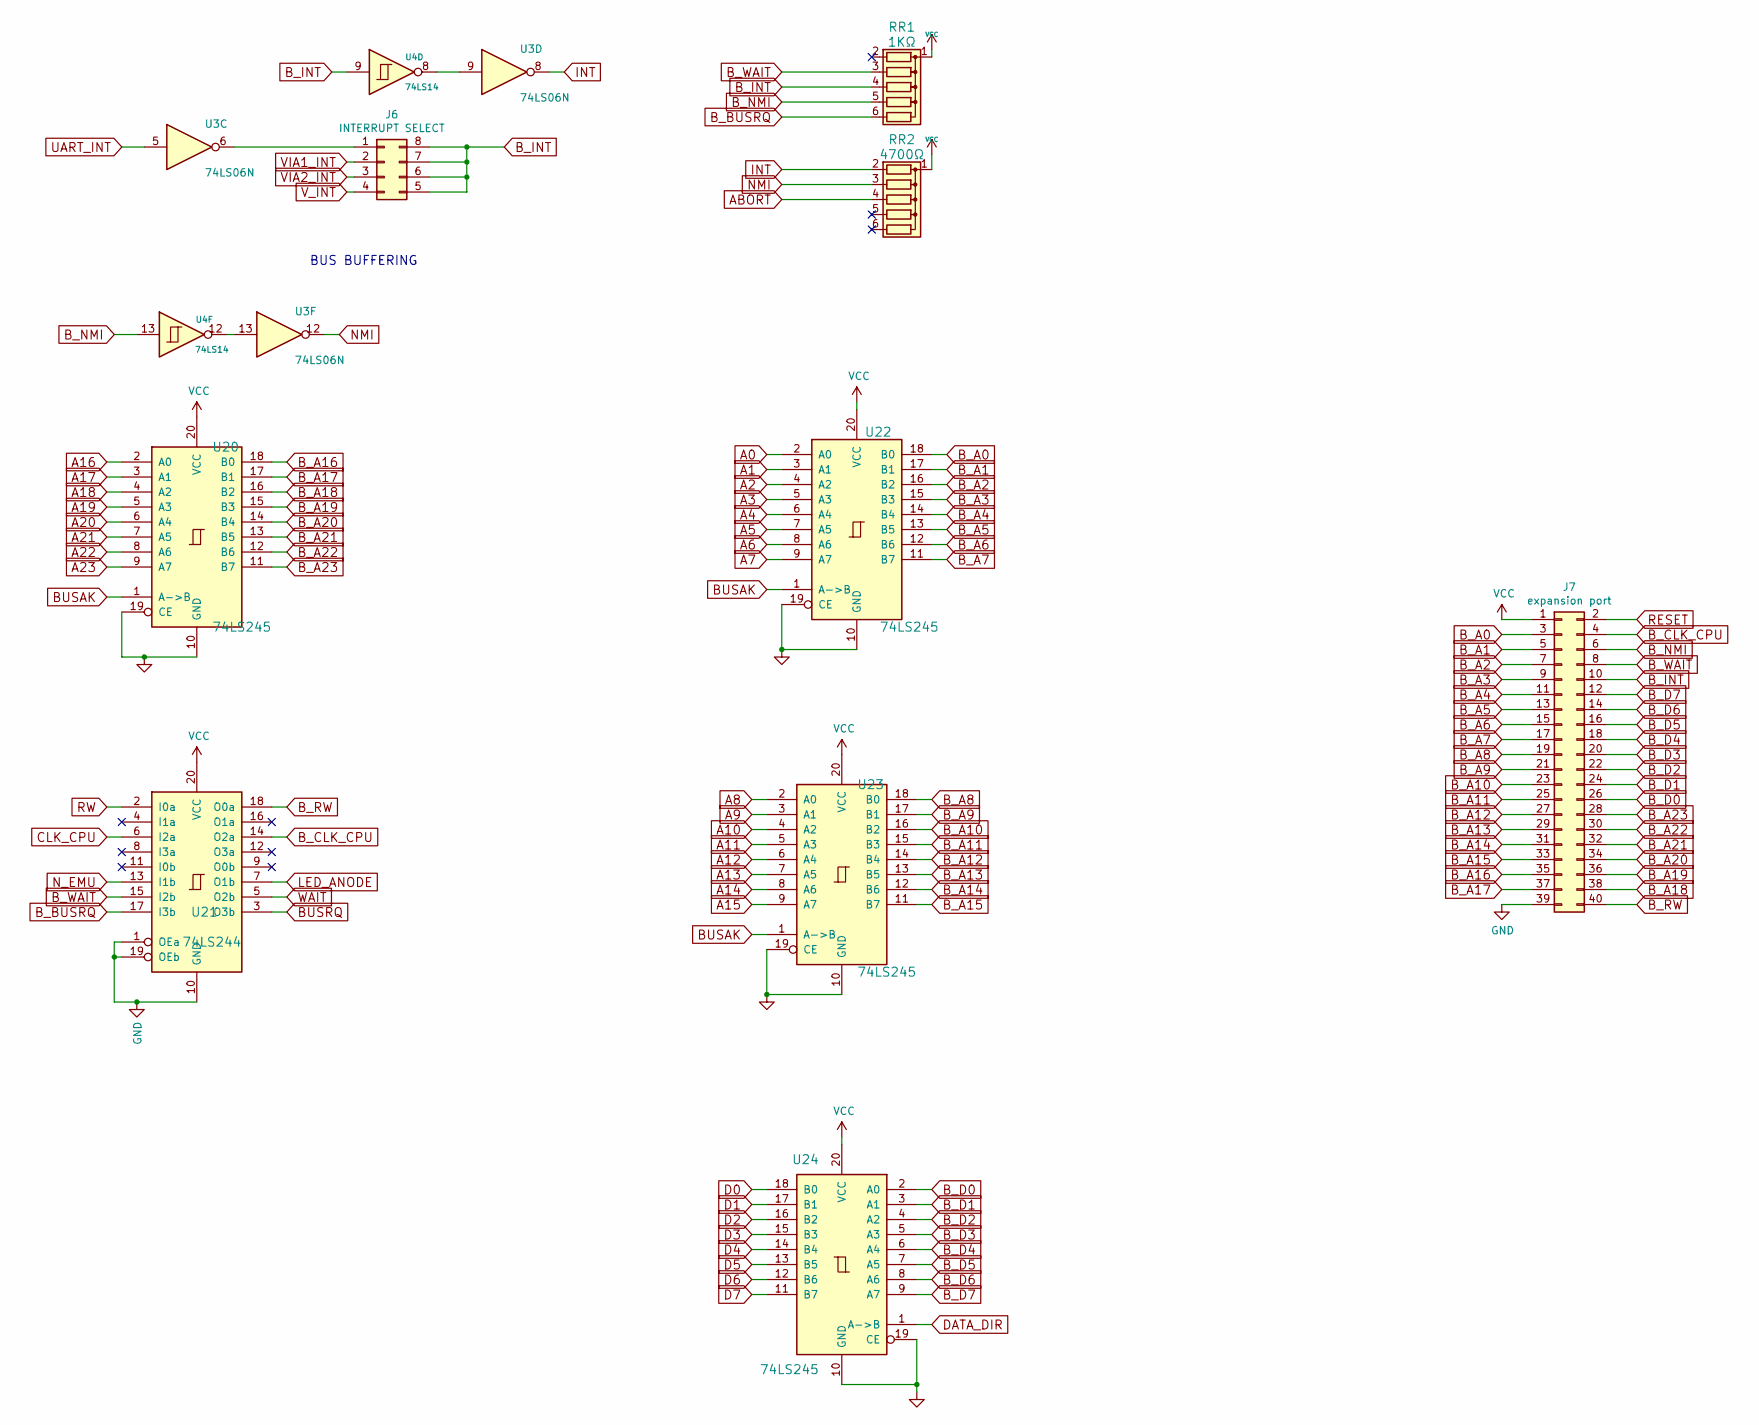
[picture p65: schematic file60341279.kicad_sch]

Parts:
J6: INTERRUPT SELECT; PinHeader_2x04_P2.54mm_Vertical
J7: expansion port; PinSocket_2x20_P2.54mm_Horizontal
RR1: 1KΩ; R_Array_SIP6
RR2: 4700Ω; R_Array_SIP6
U3: 74LS06N; DIP-14_W7.62mm_Socket
U4: 74LS14; DIP-14_W7.62mm_Socket_LongPads
U20, U22, U23, U24: 74LS245; DIP-20_W7.62mm_Socket_LongPads
U21: 74LS244; DIP-20_W7.62mm_Socket_LongPads

Connections:
A0: U22.2 (A0)
A1: U22.3 (A1)
A2: U22.4 (A2)
A3: U22.5 (A3)
A4: U22.6 (A4)
A5: U22.7 (A5)
A6: U22.8 (A6)
A7: U22.9 (A7)
A8: U23.2 (A0)
A9: U23.3 (A1)
A10: U23.4 (A2)
A11: U23.5 (A3)
A12: U23.6 (A4)
A13: U23.7 (A5)
A14: U23.8 (A6)
A15: U23.9 (A7)
A16: U20.2 (A0)
A17: U20.3 (A1)
A18: U20.4 (A2)
A19: U20.5 (A3)
A20: U20.6 (A4)
A21: U20.7 (A5)
A22: U20.8 (A6)
A23: U20.9 (A7)
ABORT: RR2.4 (R3)
BUSAK: U20.1 (A->B), U22.1 (A->B), U23.1 (A->B)
BUSRQ: U21.3 (O3b)
B_A0: J7.3, U22.18 (B0)
B_A1: J7.5, U22.17 (B1)
B_A2: J7.7, U22.16 (B2)
B_A3: J7.9, U22.15 (B3)
B_A4: J7.11, U22.14 (B4)
B_A5: J7.13, U22.13 (B5)
B_A6: J7.15, U22.12 (B6)
B_A7: J7.17, U22.11 (B7)
B_A8: J7.19, U23.18 (B0)
B_A9: J7.21, U23.17 (B1)
B_A10: J7.23, U23.16 (B2)
B_A11: J7.25, U23.15 (B3)
B_A12: J7.27, U23.14 (B4)
B_A13: J7.29, U23.13 (B5)
B_A14: J7.31, U23.12 (B6)
B_A15: J7.33, U23.11 (B7)
B_A16: J7.35, U20.18 (B0)
B_A17: J7.37, U20.17 (B1)
B_A18: J7.38, U20.16 (B2)
B_A19: J7.36, U20.15 (B3)
B_A20: J7.34, U20.14 (B4)
B_A21: J7.32, U20.13 (B5)
B_A22: J7.30, U20.12 (B6)
B_A23: J7.28, U20.11 (B7)
B_BUSRQ: RR1.6 (R5), U21.17 (I3b)
B_CLK_CPU: J7.4, U21.14 (O2a)
B_D0: J7.26, U24.2 (A0)
B_D1: J7.24, U24.3 (A1)
B_D2: J7.22, U24.4 (A2)
B_D3: J7.20, U24.5 (A3)
B_D4: J7.18, U24.6 (A4)
B_D5: J7.16, U24.7 (A5)
B_D6: J7.14, U24.8 (A6)
B_D7: J7.12, U24.9 (A7)
B_INT: J6.5, J6.6, J6.7, J6.8, J7.10, RR1.4 (R3), U4.9
B_NMI: J7.6, RR1.5 (R4), U4.13
B_RW: J7.40, U21.18 (O0a)
B_WAIT: J7.8, RR1.3 (R2), U21.15 (I2b)
CLK_CPU: U21.6 (I2a)
D0: U24.18 (B0)
D1: U24.17 (B1)
D2: U24.16 (B2)
D3: U24.15 (B3)
D4: U24.14 (B4)
D5: U24.13 (B5)
D6: U24.12 (B6)
D7: U24.11 (B7)
DATA_DIR: U24.1 (A->B)
GND: J7.39, U20.10 (GND), U20.19 (CE), U21.1 (OEa), U21.10 (GND), U21.19 (OEb), U22.10 (GND), U22.19 (CE), U23.10 (GND), U23.19 (CE), U24.10 (GND), U24.19 (CE)
INT: RR2.2 (R1), U3.8
LED_ANODE: U21.7 (O1b)
NMI: RR2.3 (R2), U3.12
N_EMU: U21.13 (I1b)
unnamed: J6.1, U3.6
unnamed: U3.9, U4.8
unnamed: U3.13, U4.12
RESET: J7.2
RW: U21.2 (I0a)
UART_INT: U3.5
VCC: J7.1, RR1.1 (common), RR2.1 (common), U20.20 (VCC), U21.20 (VCC), U22.20 (VCC), U23.20 (VCC), U24.20 (VCC)
VIA1_INT: J6.2
VIA2_INT: J6.3
V_INT: J6.4
WAIT: U21.5 (O2b)

Notes on the sheet:
BUS BUFFERING
