danwerner21/we816/Hardware/we816.kicad_sch

## KiCad design Hardware/we816.kicad_sch (2022-08-01)

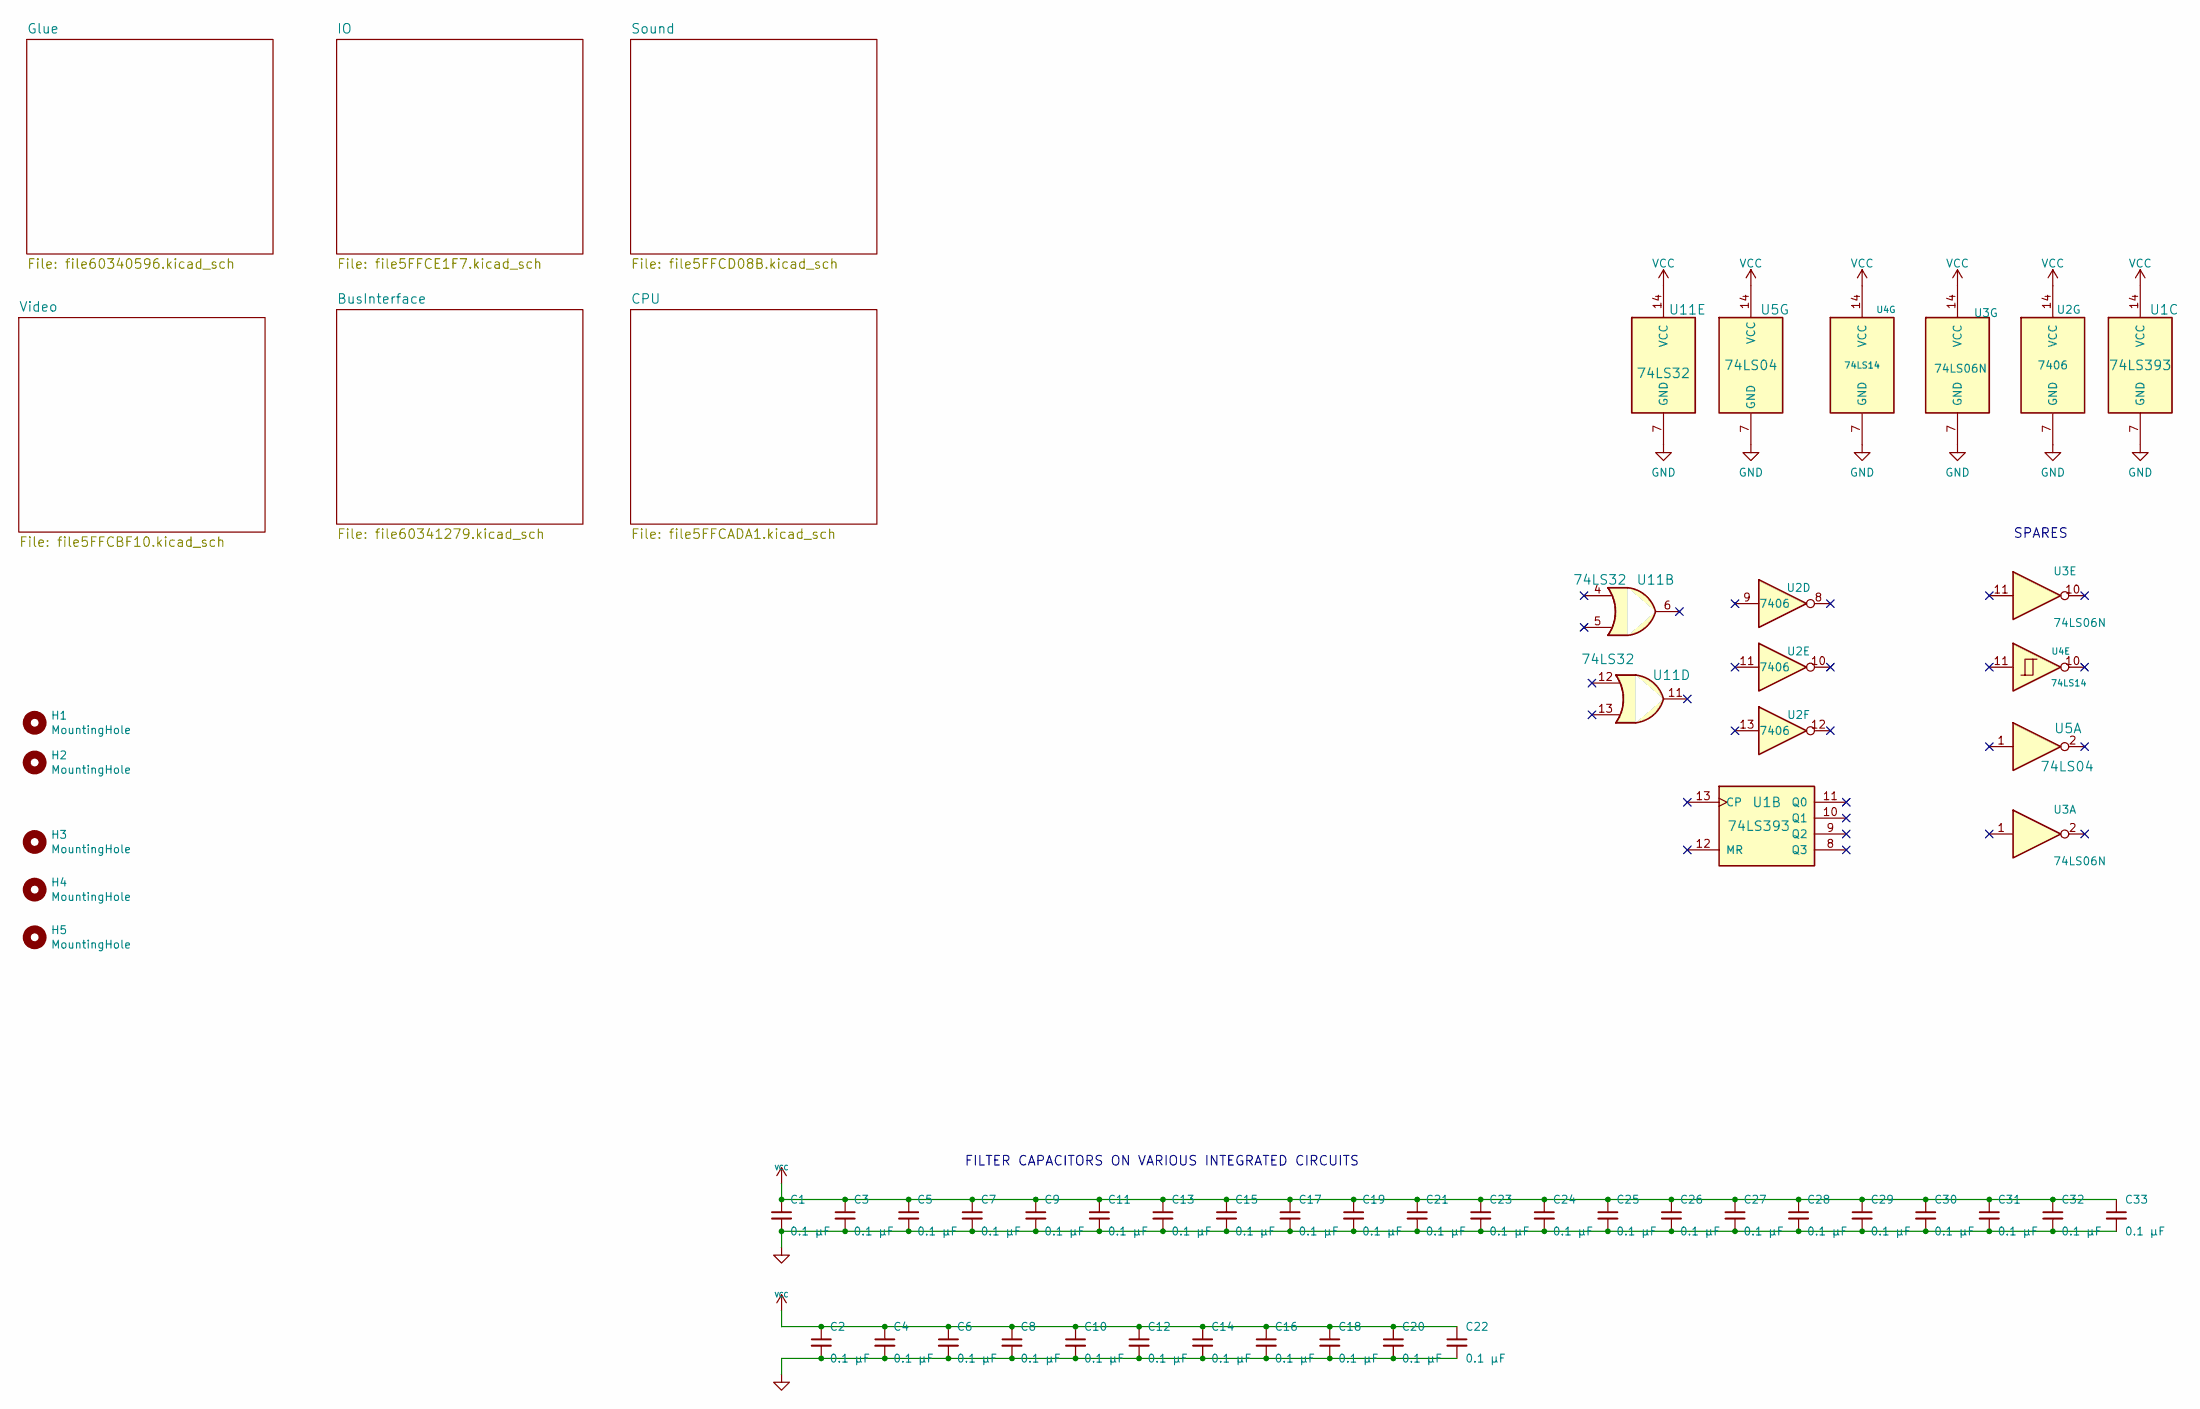
[picture p66: schematic we816.kicad_sch]

Parts:
C1, C2, C3, C4, C5, C6, C7, C8, C9, C10, C11, C12, C13, C14, C15, C16, C17, C18, C19, C20, C21, C22, C23, C24, C25, C26, C27, C28, C29, C30, C31, C32, C33: 0.1 µF; C_Rect_L7.0mm_W2.0mm_P5.00mm
H1, H2, H3, H4, H5: MountingHole; MountingHole_3.2mm_M3
U1: 74LS393; DIP-14_W7.62mm_Socket
U2: 7406; DIP-14_W7.62mm_Socket
U3: 74LS06N; DIP-14_W7.62mm_Socket
U4: 74LS14; DIP-14_W7.62mm_Socket_LongPads
U5: 74LS04; DIP-14_W7.62mm_Socket
U11: 74LS32; DIP-14_W7.62mm_Socket

Connections:
GND: C1.2, C2.2, C3.2, C4.2, C5.2, C6.2, C7.2, C8.2, C9.2, C10.2, C11.2, C12.2, C13.2, C14.2, C15.2, C16.2, C17.2, C18.2, C19.2, C20.2, C21.2, C22.2, C23.2, C24.2, C25.2, C26.2, C27.2, C28.2, C29.2, C30.2, C31.2, C32.2, C33.2, U1.7 (GND), U2.7 (GND), U3.7 (GND), U4.7 (GND), U5.7 (GND), U11.7 (GND)
VCC: C1.1, C2.1, C3.1, C4.1, C5.1, C6.1, C7.1, C8.1, C9.1, C10.1, C11.1, C12.1, C13.1, C14.1, C15.1, C16.1, C17.1, C18.1, C19.1, C20.1, C21.1, C22.1, C23.1, C24.1, C25.1, C26.1, C27.1, C28.1, C29.1, C30.1, C31.1, C32.1, C33.1, U1.14 (VCC), U2.14 (VCC), U3.14 (VCC), U4.14 (VCC), U5.14 (VCC), U11.14 (VCC)

Notes on the sheet:
FILTER CAPACITORS ON VARIOUS INTEGRATED CIRCUITS
SPARES
