danwerner21/we816/firmware/fonttms-1.asm

			 ; Font file from FontEditor
 .DB $00,$00,$00,$00,$00,$00,$00,$00, ; $FF
 .DB $FC,$FC,$FC,$FC,$FC,$FC,$FC,$FC, ; $FE
 .DB $00,$F8,$80,$40,$3C,$F0,$00,$00, ; $FD
 .DB $00,$48,$48,$48,$B0,$00,$00,$00, ; $FC
 .DB $00,$08,$18,$28,$48,$08,$08,$0C, ; $FB
 .DB $00,$00,$00,$00,$00,$38,$00,$00, ; $FA
 .DB $00,$00,$00,$00,$00,$38,$38,$00, ; $F9
 .DB $00,$00,$00,$00,$38,$44,$44,$38, ; $F8
 .DB $00,$00,$98,$64,$00,$98,$64,$00, ; $F7
 .DB $00,$30,$30,$00,$FC,$00,$30,$30, ; $F6
 .DB $70,$B0,$30,$30,$30,$30,$30,$30, ; $F5
 .DB $30,$30,$30,$30,$30,$30,$34,$18, ; $F4
 .DB $00,$FC,$00,$10,$20,$40,$20,$10, ; $F3
 .DB $00,$FC,$00,$20,$10,$08,$10,$20, ; $F2
 .DB $00,$FC,$00,$10,$10,$7C,$10,$10, ; $F1
 .DB $00,$FC,$00,$00,$FC,$00,$00,$FC, ; $F0
 .DB $00,$CC,$CC,$CC,$CC,$30,$00,$00, ; $EF
 .DB $00,$38,$40,$80,$F8,$80,$40,$38, ; $EE
 .DB $00,$70,$68,$58,$38,$00,$00,$00, ; $ED
 .DB $00,$00,$6C,$90,$90,$6C,$00,$00, ; $EC
 .DB $00,$38,$44,$44,$44,$38,$40,$3C, ; $EB
 .DB $00,$84,$48,$48,$84,$84,$84,$78, ; $EA
 .DB $00,$38,$CC,$CC,$FC,$CC,$CC,$30, ; $E9
 .DB $00,$FC,$10,$38,$44,$38,$10,$FC, ; $E8
 .DB $00,$1C,$10,$10,$98,$74,$00,$00, ; $E7
 .DB $80,$70,$88,$88,$88,$00,$00,$00, ; $E6
 .DB $00,$70,$88,$88,$7C,$00,$00,$00, ; $E5
 .DB $00,$F8,$88,$40,$20,$40,$88,$F8, ; $E4
 .DB $00,$00,$48,$50,$50,$50,$50,$F8, ; $E3
 .DB $00,$80,$80,$80,$80,$80,$90,$F0, ; $E2
 .DB $40,$F0,$88,$88,$B0,$88,$88,$70, ; $E1
 .DB $00,$68,$90,$90,$68,$00,$00,$00, ; $E0
 .DB $00,$FC,$FC,$FC,$0C,$0C,$0C,$0C, ; $DF
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
 .DB $30,$30,$30,$30,$30,$30,$30,$30, ; $05
 .DB $00,$00,$00,$F0,$F0,$30,$30,$30, ; $04
 .DB $00,$00,$00,$3C,$3C,$30,$30,$30, ; $03
 .DB $30,$30,$30,$F0,$F0,$00,$00,$00, ; $02
 .DB $30,$30,$30,$3C,$3C,$00,$00,$00, ; $01
 .DB $A8,$54,$A8,$54,$A8,$54,$A8,$54, ; $00
