danwerner21/we816/firmware/fonttms-2.asm

FONT_TMS:
 .DB $00,$00,$78,$78,$78,$78,$00,$00 ; $FE
 .DB $00,$00,$00,$00,$70,$20,$10,$60 ; $FD
 .DB $00,$00,$00,$00,$28,$28,$28,$50 ; $FC
 .DB $00,$20,$50,$50,$10,$10,$1C,$00 ; $FB
 .DB $00,$00,$00,$00,$20,$00,$00,$00 ; $FA
 .DB $00,$00,$00,$30,$30,$00,$00,$00 ; $F9
 .DB $00,$00,$00,$00,$30,$48,$48,$30 ; $F8
 .DB $00,$00,$50,$28,$00,$50,$28,$00 ; $F7
 .DB $00,$00,$10,$00,$7C,$00,$10,$00 ; $F6
 .DB $00,$20,$50,$10,$10,$10,$10,$10 ; $F5
 .DB $10,$10,$10,$10,$10,$14,$08,$00 ; $F4
 .DB $00,$78,$00,$08,$30,$40,$30,$08 ; $F3
 .DB $00,$78,$00,$40,$30,$08,$30,$40 ; $F2
 .DB $00,$00,$38,$00,$10,$38,$10,$00 ; $F1
 .DB $00,$00,$78,$00,$78,$00,$78,$00 ; $F0
 .DB $00,$00,$48,$48,$48,$48,$30,$00 ; $EF
 .DB $00,$00,$38,$40,$78,$40,$38,$00 ; $EE
 .DB $00,$10,$38,$54,$54,$38,$10,$00 ; $ED
 .DB $00,$00,$28,$54,$54,$28,$00,$00 ; $EC
 .DB $00,$30,$48,$38,$10,$20,$40,$30 ; $EB
 .DB $00,$6C,$28,$28,$44,$44,$38,$00 ; $EA
 .DB $00,$30,$48,$48,$78,$48,$48,$30 ; $E9
 .DB $00,$38,$10,$38,$44,$38,$10,$38 ; $E8
 .DB $00,$10,$10,$10,$50,$28,$00,$00 ; $E7
 .DB $40,$40,$70,$48,$48,$48,$00,$00 ; $E6
 .DB $00,$00,$30,$48,$48,$3C,$00,$00 ; $E5
 .DB $00,$78,$48,$20,$10,$20,$48,$78 ; $E4
 .DB $00,$28,$28,$28,$28,$28,$7C,$00 ; $E3
 .DB $00,$40,$40,$40,$40,$40,$48,$78 ; $E2
 .DB $40,$70,$48,$48,$70,$48,$70,$00 ; $E1
 .DB $00,$00,$34,$48,$48,$34,$00,$00 ; $E0
 .DB $00,$00,$00,$00,$FC,$FC,$FC,$FC ; $DF
 .DB $1C,$1C,$1C,$1C,$1C,$1C,$1C,$1C ; $DE
 .DB $E0,$E0,$E0,$E0,$E0,$E0,$E0,$E0 ; $DD
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
 .DB $00,$10,$7C,$7C,$10,$38,$38,$10 ; $05
 .DB $00,$10,$38,$7C,$7C,$38,$10,$00 ; $04
 .DB $00,$10,$38,$7C,$7C,$7C,$28,$00 ; $03
 .DB $00,$38,$7C,$44,$7C,$54,$7C,$38 ; $02
 .DB $00,$38,$44,$54,$44,$6C,$44,$38 ; $01
 .DB $00,$00,$00,$00,$00,$00,$00,$00 ; $00
 FONT_TMS_END:
