danwerner21/we816/firmware/supermon816.asm

		CHIP	65816		; SET CHIP
		LONGA	OFF		; ASSUME EMULATION MODE
		LONGI	OFF		;
		PW	128
		PL 	60
		INCLIST ON

;* * * * * * * * * * * * * * * * * * * * * * * * * * * * * * * * * * * * * * * * * *
;*                                                                                 *
;*      SUPERMON 816 MACHINE LANGUAGE MONITOR FOR THE W65C816S MICROPROCESSOR      *
;* ------------------------------------------------------------------------------- *
;*      Copyright ©1991-2014 by BCS Technology Limited.  All rights reserved.      *
;*                                                                                 *
;* Permission is hereby granted to use, copy, modify and distribute this software, *
;* provided this copyright notice remains in the source code and  proper  attribu- *
;* tion is given.  Redistribution, regardless of form, must be at no charge to the *
;* end  user.  This code or any part thereof, including any derivation, MAY NOT be *
;* incorporated into any package intended for sale,  unless written permission has *
;* been given by the copyright holder.                                             *
;*                                                                                 *
;* THERE IS NO WARRANTY OF ANY KIND WITH THIS SOFTWARE.  The user assumes all risk *
;* in connection with the incorporation of this software into any system.          *
;* ------------------------------------------------------------------------------- *
;* Supermon 816 is a salute to Jim Butterfield, who passed away on June 29, 2007.  *
;*                                                                                 *
;* Jim, who was the unofficial  spokesman for  Commodore  International during the *
;* heyday of the company's 8 bit supremacy, scratch-developed the Supermon machine *
;* language monitor for the PET & CBM computers.   When the best-selling Commodore *
;* 64 was introduced, Jim adapted his software to the new machine & gave the adap- *
;* tation the name Supermon 64.   Commodore  subsequently  integrated a customized *
;* version of Supermon 64 into the C-128 to act as the resident M/L monitor.       *
;*                                                                                 *
;* Although Supermon 816 is not an adaptation of Supermon 64,  it was  decided  to *
;* keep the Supermon name alive, since Supermon 816's general operation & user in- *
;* terface is similar to that of Supermon 64.   Supermon 816 is 100 percent native *
;* mode 65C816 code & was developed from a blank canvas.                           *
;* ------------------------------------------------------------------------------- *
;* Supermon 816 is a full featured monitor and supports the following operations:  *
;*                                                                                 *
;*     A - Assemble code                                                           *
;*     C - Compare memory regions                                                  *
;*     D - Disassemble code                                                        *
;*     F - Fill memory region (cannot span banks)                                  *
;*     G - Execute code (stops at BRK)                                             *
;*     H - Search (hunt) memory region                                             *
;*     J - Execute code as a subroutine (stops at BRK or RTS)                      *
;*     M - Dump & display memory range                                             *
;*     R - Dump & display 65C816 registers                                         *
;*     T - Copy (transfer) memory region                                           *
;*     X - Exit Supermon 816 & return to operating environment                     *
;*     > - Modify up to 32 bytes of memory                                         *
;*     ; - Modify 65C816 registers                                                 *
;*                                                                                 *
;* Supermon 816 accepts binary (%), octal (%), decimal (+) and hexadecimal ($) as  *
;* input for numeric parameters.  Additionally, the H and > operations accept an   *
;* ASCII string in place of numeric values by preceding the string with ', e.g.:   *
;*                                                                                 *
;*     h 042000 042FFF 'BCS Technology Limited                                     *
;*                                                                                 *
;* If no radix symbol is entered hex is assumed.                                   *
;*                                                                                 *
;* Numeric conversion is also available.  For example, typing:                     *
;*                                                                                 *
;*     +1234567 <CR>                                                               *
;*                                                                                 *
;* will display:                                                                   *
;*                                                                                 *
;*         $12D687                                                                 *
;*         +1234567                                                                *
;*         %04553207                                                               *
;*         %100101101011010000111                                                  *
;*                                                                                 *
;* In the above example, <CR> means the console keyboard's return or enter key.    *
;*                                                                                 *
;* All numeric values are internally processed as 32 bit unsigned integers.  Addr- *
;* esses may be entered as 8, 16 or 24 bit values.  During instruction assembly,   *
;* immediate mode operands may be forced to 16 bits by preceding the operand with  *
;* an exclamation point if the instruction can accept a 16 bit operand, e.g.:      *
;*                                                                                 *
;*     a 1f2000 lda !#4                                                            *
;*                                                                                 *
;* The above will assemble as:                                                     *
;*                                                                                 *
;*     A 1F2000  A9 04 00     LDA #$0004                                           *
;*                                                                                 *
;* Entering:                                                                       *
;*                                                                                 *
;*     a 1f2000 ldx !#+157                                                         *
;*                                                                                 *
;* will assemble as:                                                               *
;*                                                                                 *
;*     A 1F2000  A2 9D 00     LDX #$009D                                           *
;*                                                                                 *
;* Absent the ! in the operand field, the above would have been assembled as:      *
;*                                                                                 *
;*     A 1F2000  A2 9D        LDX #$9D                                             *
;*                                                                                 *
;* If an immediate mode operand is greater than $FF assembly of a 16 bit operand   *
;* is implied.                                                                     *
;* ------------------------------------------------------------------------------- *
;* A Note on the PEA & PEI Instructions                                            *
;* ------------------------------------                                            *
;*                                                                                 *
;* The Eyes and Lichty programming manual uses the following syntax for the PEA    *
;* and PEI instructions:                                                           *
;*                                                                                 *
;*     PEA <operand>                                                               *
;*     PEI (<operand>)                                                             *
;*                                                                                 *
;* The WDC data sheet that was published at the time of the 65C816's release in    *
;* 1984 does not indicate a recommended or preferred syntax for any of the above   *
;* instructions.  PEA pushes its operand to the stack and hence operates like any  *
;* other immediate mode instruction, in that the operand is the data (however, PEA *
;* doesn't affect the status register).  Similarly, PEI pushes the 16 bit value    *
;* stored at <operand> and <operand>+1, and hence operates like any other direct   *
;* (zero) page instruction, again without affecting the status register.           *
;*                                                                                 *
;* BCS Technology Limited is of the opinion that the developer of the ORCA/M as-   *
;* sembler, which is the assembler referred to in the Eyes and Lichty manual, mis- *
;* understood how PEA and PEI behave during runtime, and hence chose an incorrect  *
;* syntax for these two instructions.  This error was subsequently carried forward *
;* by Eyes and Lichty.                                                             *
;*                                                                                 *
;* Supermon 816's assembler uses the following syntax for PEA and PEI:             *
;*                                                                                 *
;*     PEA #<operand>                                                              *
;*     PEI <operand>                                                               *
;*                                                                                 *
;* The operand for PEA is treated as a 16 bit value, even if entered as an 8 bit   *
;* value.  The operand for PEI must be 8 bits.                                     *
;*                                                                                 *
;* * * * * * * * * * * * * * * * * * * * * * * * * * * * * * * * * * * * * * * * * *
;
;	* * * * * * * * * * * *
;	* VERSION INFORMATION *
;	* * * * * * * * * * * *
;
softvers .macro                ;software version - change with each revision...
         .db "1"             ;major
         .db "."
         .db "0"             ;minor
         .db "."
         .db "2"             ;revision
         .endm
;
;REVISION TABLE
;
;Ver  Rev Date    Description
;-------------------------------------------------------------------------------
;1.0  2013/11/01  A) Original derived from the POC V1.1 single-board computer
;                    firmware.
;     2013/11/04  A) Fixed a problem where the B-accumulator wasn't always being
;                    be copied to shadow storage after return from execution of
;                    a J command.
;     2017/10/07  A) Converted to use WDC's 65816 assembler (D.WERNER)
;		  B) Adapt for the RBC 65c816 SBC
;		  C) Disable X command
;-------------------------------------------------------------------------------
;
;
;	        COMMENT ABBREVIATIONS
;	----------------------------------------------------
;	  BCD   binary-coded decimal
;	   DP   direct page or page zero
;	  EOF   end-of-field
;	  EOI   end-of-input
;	  LSB   least significant byte/bit
;	  LSD   least significant digit
;	  LSN   least significant nybble
;	  LSW   least significant word
;	  MPU   microprocessor
;	  MSB   most significant byte/bit
;	  MSD   most significant digit
;	  MSN   most significant nybble
;	  MSW   most-significant word
;	  RAM   random access memory
;	   WS   whitespace, i.e., blanks & horizontal tabs
;	----------------------------------------------------
;	A word is defined as 16 bits.
;
;	   MPU REGISTER SYMBOLS
;	--------------------------
;	   .A   accumulator LSB
;	   .B   accumulator MSB
;	   .C   16 bit accumulator
;	   .X   X-index
;	   .Y   Y-index
;	   DB   data bank
;	   DP   direct page
;	   PB   program bank
;	   PC   program counter
;	   SP   stack pointer
;	   SR   MPU status
;	----------------------------
;
;	  MPU STATUS REGISTER SYMBOLS
;	-------------------------------
;	    C   carry
;	    D   decimal mode
;	    I   maskable interrupts
;	    m   accumulator/memory size
;	    N   result negative
;	    V   sign overflow
;	    x   index registers size
;	    Z   result zero
;	-------------------------------
;
;================================================================================
;
;SYSTEM INTERFACE DEFINITIONS
;
;	------------------------------------------------------------------
;	This section defines the interface between Supermon 816 & the host
;	system.   Change these definitions to suit your system, but do not
;	change any label names.  All definitions must have valid values in
;	order to assemble Supermon 816.
;	------------------------------------------------------------------
;
;	--------------------------------------------------------
	;.org  $008000              ;assembly address...
SUPERMON 	SECTION 	OFFSET $8000
;
;	Set _ORIGIN_ to Supermon 816's desired assembly address.
;	--------------------------------------------------------
;
;	------------------------------------------------------------------------
;vecexit  .EQU $002000              ;exit to environment address...
;
;	Set VECEXIT to where Supermon 816 should go when it exits.  Supermon 816
;	will do a JML (long jump) to this address, which means VECEXIT must be a
;	24 bit address.
;	------------------------------------------------------------------------
;
;	------------------------------------------------------------------------
;
;getcha                  ;get keystroke from console...
;
;	GETCHA refers to an operating system API call that returns a keystroke
;	in the 8 bit accumulator.  Supermon 816  assumes that GETCHA is a non-
;	blocking subroutine & returns with carry clear to indicate that a key-
;	stroke is in .A, or with carry set to indicate that no keystroke was
;	available.  GETCHA will be called with a JSR instruction.
;
;	Supermon 816 expects .X & .Y to be preserved upon return from GETCHA.
;	You may have to modify Supermon 816 at all calls to GETCHA if your "get
;	keystroke" routine works differently than described.
;	------------------------------------------------------------------------
getcha 		.equ $FF74
CURSOR          .equ $FF86
UNCURSOR        .equ $FF89
;------------------------------------------------------------------------
;putcha   print character on console...
;
;	PUTCHA refers to an operating system API call that prints a character to
;	the console screen.  The character to be printed will be in .A, which
;	will be set to 8-bit width.  Supermon 816 assumes that PUTCHA will block
;	until the character can be processed.  PUTCHA will be called with a JSR
;	instructions.
;
;	Supermon 816 expects .X & .Y to be preserved upon return from PUTCHA.
;	You may have to modify Supermon 816 at all calls to PUTCHA if your "put
;	character" routine works differently than described.
;
putcha 		.equ $FF71
;
;	------------------------------------------------------------------------
;
;	------------------------------------------------------------------------
vecbrki  .EQU  $0302                ;BRK handler indirect vector...
;
;	Supermon 816 will modify this vector so that execution of a BRK instruc-
;	tion is intercepted & the registers  are  captured.   Your BRK front end
;	should jump through this vector after pushing the registers as follows:
;
;	         phb                   ;save DB
;	         phd                   ;save DP
;	         rep #%00110000        ;16 bit registers
;	         pha
;	         phx
;	         phy
;	         jmp (vecbrki)         ;indirect vector
;
;	When a G or J command is issued, the above sequence will be reversed be-
;	fore a jump is made to the code to be executed.  Upon exit from Supermon
;	816, the original address at VECBRKI will be restored.
;
;	If your BRK front end doesn't conform to the above you will have to mod-
;	ify Supermon 816 to accommodate the differences.  The most likely needed
;	changes will be in the order in which registers are pushed to the stack.
;	------------------------------------------------------------------------
;
;	------------------------------------------------------------------------
hwstack  .EQU $7FFF                ;top of hardware stack...
;
;	Supermon 816 initializes the stack pointer to this address when the cold
;	start at MONCOLD is called to enter the monitor.  The stack pointer will
;	be undisturbed when entry into Supermon 816 is through JMONBRK (see jump
;	table definitions).
;	------------------------------------------------------------------------
;
;	------------------------------------------------------------------------
zeropage .EQU $10                  ;Supermon 816's direct page...
;
;	Supermon 816 uses direct page starting at this address.  Be sure that no
;	conflict occurs with other software.
;	------------------------------------------------------------------------
;
;	------------------------------------------------------------------------
stopkey  .EQU $03                  ;display abort key...
;
;	Supermon 816 will poll for a "stop key" during display operations, such
;	as code disassembly & memory dumps, so as to abort further processing &
;	return to the command prompt.  STOPKEY must be defined with the ASCII
;	value that the "stop key" will emit when typed.  The polling is via a
;	call to GETCHA (described above).  The default STOPKEY definition of $03
;	is for ASCII <ETX> or [Ctrl-C].
;	------------------------------------------------------------------------
;
ibuffer  .EQU $000200               ;input buffer &...
auxbuf   .EQU ibuffer+s_ibuf+s_byte ;auxiliary buffer...
;
;	------------------------------------------------------------------------
;	Supermon 816 will use the above definitions for input buffers.  These
;	buffers may be located anywhere in RAM that is convenient.  The buffers
;	are stateless, which means that unless Supermon 816 has control of your
;	system, they may be overwritten without consequence.
;	------------------------------------------------------------------------
;
;================================================================================
;
;W65C816S INSTRUCTION SYNTHESIS MACROS -- !!!!! DO NOT EDIT !!!!!
;


_asm24_  .macro _ad
         .db <_ad,>_ad,_ad>>16
         .endm

;brl      .macro _ad
;_ba      =*+3
;         .db $82
;         .dw _ad-_ba
;         .endm
;
;jml      .macro _ad
;         .db $5c
;         _asm24_ _ad
;         .endm
;
;mvn      .macro _s,_d
;         .db $54,_d,_s
;         .endm
;
;mvp      .macro _s,_d
;         .db $44,_d,_s
;         .endm
;
;pea      .macro _op
;         .db $f4
;         .dw _op
;         .endm
;
;phb      .macro
;         .db $8b
;         .endm
;
;phk      .macro
;         .db $4b
;         .endm
;
;plb      .macro
;         .db $ab
;         .endm
;
;rep      .macro _op
;         .db $c2,_op
;         .endm
;
;sep      .macro _op
;         .db $e2,_op
;         .endm
;
;tcd      .macro
;         .db $5b
;         .endm
;
;tcs      .macro
;         .db $1b
;         .endm
;
;tdc      .macro
;         .db $7b
;         .endm
;
;tsc      .macro
;         .db $3b
;         .endm
;
;txy      .macro
;         .db $9b
;         .endm
;
;tyx      .macro
;         .db $bb
;         .endm
;
;wai      .macro
;         .db $cb
;        .endm
;
;xba      .macro
;         .db $eb
;         .endm
;
adcw     .macro _op
         adc #<_op
         .db >_op
         .endm
;
andw     .macro _op
         and #<_op
         .db >_op
         .endm
;
bitw     .macro _op
         bit #<_op
         .db >_op
         .endm
;
cmpw     .macro _op
         cmp #<_op
         .db >_op
         .endm
;
cpxw     .macro _op
         cpx #<_op
         .db >_op
         .endm
;
cpyw     .macro _op
         cpy #<_op
         .db >_op
         .endm
;
eorw     .macro _op
         eor #<_op
         .db >_op
         .endm
;
ldaw     .macro _op
         lda #<_op
         .db >_op
         .endm
;
ldxw     .macro _op
         ldx #<_op
         .db >_op
         .endm
;
ldyw     .macro _op
         ldy #<_op
         .db >_op
         .endm
;
oraw     .macro _op
         ora #<_op
         .db >_op
         .endm
;
sbcw     .macro _op
         sbc #<_op
         .db >_op
         .endm
;
ldalx    .macro _ad
         .db $bf
         _asm24_ _ad
         .endm
;
adcil    .macro _ad
         .db $67,_ad
         .endm
;
adcily   .macro _ad
         .db $77,_ad
         .endm
;
andil    .macro _ad
         .db $27,_ad
         .endm
;
andily   .macro _ad
         .db $37,_ad
         .endm
;
cmpil    .macro _ad
         .db $c7,_ad
         .endm
;
cmpily   .macro _ad
         .db $d7,_ad
         .endm
;
eoril    .macro _ad
         .db $47,_ad
         .endm
;
eorily   .macro _ad
         .db $57,_ad
         .endm
;
ldail    .macro _ad
         .db $a7,_ad
         .endm
;
ldaily   .macro _ad
         .db $b7,_ad
         .endm
;
orail    .macro _ad
         .db $07,_ad
         .endm
;
oraily   .macro _ad
         .db $17,_ad
         .endm
;
sbcil    .macro _ad
         .db $e7,_ad
         .endm
;
sbcily   .macro _ad
         .db $f7,_ad
         .endm
;
stail    .macro _ad
         .db $87,_ad
         .endm
;
staily   .macro _ad
         .db $97,_ad
         .endm
;
adcs     .macro _of
         .db $63,_of
         .endm
;
adcsi    .macro _of
         .db $73,_of
         .endm
;
ands     .macro _of
         .db $23,_of
         .endm
;
andsi    .macro _of
         .db $33,_of
         .endm
;
cmps     .macro _of
         .db $c3,_of
         .endm
;
cmpsi    .macro _of
         .db $d3,_of
         .endm
;
eors     .macro _of
         .db $43,_of
         .endm
;
eorsi    .macro _of
         .db $53,_of
         .endm
;
ldas     .macro _of
         .db $a3,_of
         .endm
;
ldasi    .macro _of
         .db $b3,_of
         .endm
;
oras     .macro _of
         .db $03,_of
         .endm
;
orasi    .macro _of
         .db $13,_of
         .endm
;
sbcs     .macro _of
         .db $e3,_of
         .endm
;
sbcsi    .macro _of
         .db $f3,_of
         .endm
;
stas     .macro _of
         .db $83,_of
         .endm
;
stasi    .macro _of
         .db $93,_of
         .endm
;
slonga    .macro
         .db $c2,$20
         .endm
;
longr    .macro
         .db $c2,$30
         .endm
;
longx    .macro
         .db $c2,$10
         .endm
;
shorta   .macro
         .db $e2,$20
         .endm
;
shorti   .macro
         .db $e2,$10
         .endm
;
shortr   .macro
         .db $e2,$30
         .endm
;
shortx   .macro
         .db $e2,$10
         .endm
;
;================================================================================
;
;CONSOLE DISPLAY CONTROL MACROS
;
;	------------------------------------------------------------------------
;	The following macros execute terminal  control procedures  that  perform
;	such tasks as clearing the screen,  switching  between  normal & reverse
;	video, etc.  These macros are for WYSE 60 & compatible displays, such as
;	the WYSE 150, WYSE 160, WYSE 325 & WYSE GPT.   Only the functions needed
;	by Supermon 816 are included.
;
;	If your console is not WYSE 60 compatible, you will need to  edit  these
;	macros as required to control your particular console or terminal.  Note
;	that in some cases one macro may call another.  Exercise caution in your
;	edits to avoid introducing display bugs.
;
;	If your console display cannot execute one of these procedures,  such as
;	'CL' (clear to end of line), you will have to develop an alternative.
;	------------------------------------------------------------------------
;
;
;
;	cursor control...
;
cr       .macro                ;carriage return
         .db a_cr
         .endm
;
lf       .macro                ;carriage return/line feed
         cr
         .db a_lf
         .endm
;
;	miscellaneous control...
;
rb       .macro                ;ring "bell"
         .db a_bel
         .endm
;
;
;================================================================================
;
;ASCII CONTROL DEFINITIONS (menmonic order)
;
a_bel    .equ $07                  ;<BEL> alert/ring bell
a_bs     .equ $08                  ;<BS>  backspace
a_cr     .equ $0d                  ;<CR>  carriage return
a_del    .equ $7f                  ;<DEL> delete
a_esc    .equ $1b                  ;<ESC> escape
a_ht     .equ $09                  ;<HT>  horizontal tabulation
a_lf     .equ $0a                  ;<LF>  linefeed
;
;
;	miscellaneous (description order)...
;
a_blank  .equ ' '                  ;blank (whitespace)
a_asclch .equ 'z'                  ;end of lowercase ASCII
a_lctouc .equ $5f                  ;LC to UC conversion mask
a_asclcl .equ 'a'                  ;start of lowercase ASCII
;
;================================================================================
;
;GLOBAL ATOMIC CONSTANTS
;
;
;	data type sizes...
;
s_byte   .equ 1                    ;byte
s_word   .equ 2                    ;word (16 bits)
s_xword  .equ 3                    ;extended word (24 bits)
s_dword  .equ 4                    ;double word (32 bits)
s_rampag .equ $0100                ;65xx RAM page
;
;
;	data type sizes in bits...
;
s_bibyte .equ 8                    ;byte
s_bnybbl .equ 4                    ;nybble
;
;
;	miscellaneous...
;
bitabs   .equ $2c                  ;absolute BIT opcode
bitzp    .equ $24                  ;zero page BIT opcode
;
;================================================================================
;
;W65C816S NATIVE MODE STATUS REGISTER DEFINITIONS
;
s_mpudbx .equ s_byte               ;data bank size
s_mpudpx .equ s_word               ;direct page size
s_mpupbx .equ s_byte               ;program bank size
s_mpupcx .equ s_word               ;program counter size
s_mpuspx .equ s_word               ;stack pointer size
s_mpusrx .equ s_byte               ;status size
;
;
;	status register flags...
;
sr_car   .equ %00000001            ;C
sr_zer   .equ sr_car<<1          ;Z
sr_irq   .equ sr_zer<<1          ;I
sr_bdm   .equ sr_irq<<1          ;D
sr_ixw   .equ sr_bdm<<1          ;x
sr_amw   .equ sr_ixw<<1          ;m
sr_ovl   .equ sr_amw<<1          ;V
sr_neg   .equ sr_ovl<<1          ;N
;
;	NVmxDIZC
;	xxxxxxxx
;	||||||||
;	|||||||+---> 1 = carry set/generated
;	||||||+----> 1 = result = zero
;	|||||+-----> 1 = IRQs ignored
;	||||+------> 0 = binary arithmetic mode
;	||||         1 = decimal arithmetic mode
;	|||+-------> 0 = 16 bit index
;	|||          1 = 8 bit index
;	||+--------> 0 = 16 bit .A & memory
;	||           1 = 8 bit .A & memory
;	|+---------> 1 = sign overflow
;	+----------> 1 = result = negative
;
;================================================================================
;
;"SIZE-OF" CONSTANTS
;
s_addr   .equ s_xword              ;24 bit address
s_auxbuf .equ 32                   ;auxiliary buffer
s_ibuf   .equ 69                   ;input buffer
s_mnemon .equ 3                    ;MPU ASCII mnemonic
s_mnepck .equ 2                    ;MPU encoded mnemonic
s_mvinst .equ 3                    ;MVN/MVP instruction
s_opcode .equ s_byte               ;MPU opcode
s_oper   .equ s_xword              ;operand
s_pfac   .equ s_dword              ;primary math accumulator
s_sfac   .equ s_dword+s_word       ;secondary math accumulators
;
;================================================================================
;
;"NUMBER-OF" CONSTANTS
;
n_dbytes .equ 21                   ;default disassembly bytes
n_dump   .equ 8                    ;bytes per memory dump line
n_mbytes .equ s_rampag-1           ;default memory dump bytes
n_hccols .equ 10                   ;compare/hunt display columns
n_opcols .equ 3*s_oper             ;disassembly operand columns
n_opslsr .equ 4                    ;LSRs to extract instruction size
n_shfenc .equ 5                    ;shifts to encode/decode mnemonic
;
;================================================================================
;
;NUMERIC CONVERSION CONSTANTS
;
a_hexdec .equ 'A'-'9'-2            ;hex to decimal difference
c_bin    .equ '%'                  ;binary prefix
c_dec    .equ '+'                  ;decimal prefix
c_hex    .equ '$'                  ;hexadecimal prefix
c_oct    .equ '@'                  ;octal prefix
k_hex    .equ 'f'                  ;hex ASCII conversion
m_bits   .equ s_pfac*s_bibyte      ;operand bit size
m_cbits  .equ s_sfac*s_bibyte      ;workspace bit size
bcdumask .equ %00001111            ;isolate BCD units mask
btoamask .equ %00110000            ;binary to ASCII mask
;
;================================================================================
;
;ASSEMBLER/DISASSEMBLER CONSTANTS
;
a_mnecvt .equ '?'                  ;encoded mnemonic conversion base
aimmaska .equ %00011111            ;.A immediate opcode test #1
aimmaskb .equ %00001001            ;.A immediate opcode test #2
asmprfx  .equ 'A'                  ;assemble code prefix
ascprmct .equ 9                    ;assembler prompt "size-of"
disprfx  .equ '.'                  ;disassemble code prefix
flimmask .equ %11000000            ;force long immediate flag
opc_cpxi .equ $e0                  ;CPX # opcode
opc_cpyi .equ $c0                  ;CPY # opcode
opc_ldxi .equ $a2                  ;LDX # opcode
opc_ldyi .equ $a0                  ;LDY # opcode
opc_mvn  .equ $54                  ;MVN opcode
opc_mvp  .equ $44                  ;MVP opcode
opc_rep  .equ $c2                  ;REP opcode
opc_sep  .equ $e2                  ;SEP opcode
pfmxmask .equ sr_amw|sr_ixw      ;MPU m & x flag bits mask
;
;
;	assembler prompt buffer offsets...
;
apadrbkh .equ s_word               ;instruction address bank MSN
apadrbkl .equ apadrbkh+s_byte      ;instruction address bank LSN
apadrmbh .equ apadrbkl+s_byte      ;instruction address MSB MSN
apadrmbl .equ apadrmbh+s_byte      ;instruction address MSB LSN
apadrlbh .equ apadrmbl+s_byte      ;instruction address LSB MSN
apadrlbl .equ apadrlbh+s_byte      ;instruction address LSB LSN
;
;
;	addressing mode preamble symbols...
;
amp_flim .equ '!'                  ;force long immediate
amp_imm  .equ '#'                  ;immediate
amp_ind  .equ '('                  ;indirect
amp_indl .equ '['                  ;indirect long
;
;
;	addressing mode symbolic translation indices...
;
am_nam   .equ %0000                ;no symbol
am_imm   .equ %0001                ;#
am_adrx  .equ %0010                ;<addr>,X
am_adry  .equ %0011                ;<addr>,Y
am_ind   .equ %0100                ;(<addr>)
am_indl  .equ %0101                ;[<dp>]
am_indly .equ %0110                ;[<dp>],Y
am_indx  .equ %0111                ;(<addr>,X)
am_indy  .equ %1000                ;(<dp>),Y
am_stk   .equ %1001                ;<offset>,S
am_stky  .equ %1010                ;(<offset>,S),Y
am_move  .equ %1011                ;<sbnk>,<dbnk>
;
;
;	operand size translation indices...
;
ops0     .equ %0000<<4           ;no operand
ops1     .equ %0001<<4           ;8 bit operand
ops2     .equ %0010<<4           ;16 bit operand
ops3     .equ %0011<<4           ;24 bit operand
bop1     .equ %0101<<4           ;8 bit relative branch
bop2     .equ %0110<<4           ;16 bit relative branch
vops     .equ %1001<<4           ;8 or 16 bit operand
;
;
;	operand size & addressing mode extraction masks...
;
amodmask .equ %00001111            ;addressing mode index
opsmask  .equ %00110000            ;operand size
vopsmask .equ %11000000            ;BOPx & VOPS flag bits
;
;
;	instruction mnemonic encoding...
;
mne_adc  .equ $2144                ;ADC
mne_and  .equ $2bc4                ;AND
mne_asl  .equ $6d04                ;ASL
mne_bcc  .equ $2106                ;BCC
mne_bcs  .equ $a106                ;BCS
mne_beq  .equ $9186                ;BEQ
mne_bit  .equ $aa86                ;BIT
mne_bmi  .equ $5386                ;BMI
mne_bne  .equ $33c6                ;BNE
mne_bpl  .equ $6c46                ;BPL
mne_bra  .equ $14c6                ;BRA
mne_brk  .equ $64c6                ;BRK
mne_brl  .equ $6cc6                ;BRL
mne_bvc  .equ $25c6                ;BVC
mne_bvs  .equ $a5c6                ;BVS
mne_clc  .equ $2348                ;CLC
mne_cld  .equ $2b48                ;CLD
mne_cli  .equ $5348                ;CLI
mne_clv  .equ $bb48                ;CLV
mne_cmp  .equ $8b88                ;CMP
mne_cop  .equ $8c08                ;COP
mne_cpx  .equ $cc48                ;CPX
mne_cpy  .equ $d448                ;CPY
mne_dec  .equ $218a                ;DEC
mne_dex  .equ $c98a                ;DEX
mne_dey  .equ $d18a                ;DEY
mne_eor  .equ $9c0c                ;EOR
mne_inc  .equ $23d4                ;INC
mne_inx  .equ $cbd4                ;INX
mne_iny  .equ $d3d4                ;INY
mne_jml  .equ $6b96                ;JML
mne_jmp  .equ $8b96                ;JMP
mne_jsl  .equ $6d16                ;JSL
mne_jsr  .equ $9d16                ;JSR
mne_lda  .equ $115a                ;LDA
mne_ldx  .equ $c95a                ;LDX
mne_ldy  .equ $d15a                ;LDY
mne_lsr  .equ $9d1a                ;LSR
mne_mvn  .equ $7ddc                ;MVN
mne_mvp  .equ $8ddc                ;MVP
mne_nop  .equ $8c1e                ;NOP
mne_ora  .equ $14e0                ;ORA
mne_pea  .equ $11a2                ;PEA
mne_pei  .equ $51a2                ;PEI
mne_per  .equ $99a2                ;PER
mne_pha  .equ $1262                ;PHA
mne_phb  .equ $1a62                ;PHB
mne_phd  .equ $2a62                ;PHD
mne_phk  .equ $6262                ;PHK
mne_php  .equ $8a62                ;PHP
mne_phx  .equ $ca62                ;PHX
mne_phy  .equ $d262                ;PHY
mne_pla  .equ $1362                ;PLA
mne_plb  .equ $1b62                ;PLB
mne_pld  .equ $2b62                ;PLD
mne_plp  .equ $8b62                ;PLP
mne_plx  .equ $cb62                ;PLX
mne_ply  .equ $d362                ;PLY
mne_rep  .equ $89a6                ;REP
mne_rol  .equ $6c26                ;ROL
mne_ror  .equ $9c26                ;ROR
mne_rti  .equ $5566                ;RTI
mne_rtl  .equ $6d66                ;RTL
mne_rts  .equ $a566                ;RTS
mne_sbc  .equ $20e8                ;SBC
mne_sec  .equ $21a8                ;SEC
mne_sed  .equ $29a8                ;SED
mne_sei  .equ $51a8                ;SEI
mne_sep  .equ $89a8                ;SEP
mne_sta  .equ $1568                ;STA
mne_stp  .equ $8d68                ;STP
mne_stx  .equ $cd68                ;STX
mne_sty  .equ $d568                ;STY
mne_stz  .equ $dd68                ;STZ
mne_tax  .equ $c8aa                ;TAX
mne_tay  .equ $d0aa                ;TAY
mne_tcd  .equ $292a                ;TCD
mne_tcs  .equ $a12a                ;TCS
mne_tdc  .equ $216a                ;TDC
mne_trb  .equ $1cea                ;TRB
mne_tsb  .equ $1d2a                ;TSB
mne_tsc  .equ $252a                ;TSC
mne_tsx  .equ $cd2a                ;TSX
mne_txa  .equ $166a                ;TXA
mne_txs  .equ $a66a                ;TXS
mne_txy  .equ $d66a                ;TXY
mne_tya  .equ $16aa                ;TYA
mne_tyx  .equ $ceaa                ;TYX
mne_wai  .equ $50b0                ;WAI
mne_wdm  .equ $7170                ;WDM
mne_xba  .equ $10f2                ;XBA
mne_xce  .equ $3132                ;XCE
;
;
;	encoded instruction mnemonic indices...
;
mne_adcx .equ 16                   ;ADC
mne_andx .equ 29                   ;AND
mne_aslx .equ 44                   ;ASL
mne_bccx .equ 15                   ;BCC
mne_bcsx .equ 65                   ;BCS
mne_beqx .equ 59                   ;BEQ
mne_bitx .equ 70                   ;BIT
mne_bmix .equ 36                   ;BMI
mne_bnex .equ 31                   ;BNE
mne_bplx .equ 42                   ;BPL
mne_brax .equ 5                    ;BRA
mne_brkx .equ 39                   ;BRK
mne_brlx .equ 43                   ;BRL
mne_bvcx .equ 23                   ;BVC
mne_bvsx .equ 68                   ;BVS
mne_clcx .equ 20                   ;CLC
mne_cldx .equ 27                   ;CLD
mne_clix .equ 35                   ;CLI
mne_clvx .equ 71                   ;CLV
mne_cmpx .equ 53                   ;CMP
mne_copx .equ 55                   ;COP
mne_cpxx .equ 78                   ;CPX
mne_cpyx .equ 88                   ;CPY
mne_decx .equ 18                   ;DEC
mne_dexx .equ 74                   ;DEX
mne_deyx .equ 84                   ;DEY
mne_eorx .equ 61                   ;EOR
mne_incx .equ 21                   ;INC
mne_inxx .equ 77                   ;INX
mne_inyx .equ 87                   ;INY
mne_jmlx .equ 40                   ;JML
mne_jmpx .equ 54                   ;JMP
mne_jslx .equ 45                   ;JSL
mne_jsrx .equ 63                   ;JSR
mne_ldax .equ 1                    ;LDA
mne_ldxx .equ 73                   ;LDX
mne_ldyx .equ 83                   ;LDY
mne_lsrx .equ 64                   ;LSR
mne_mvnx .equ 48                   ;MVN
mne_mvpx .equ 58                   ;MVP
mne_nopx .equ 56                   ;NOP
mne_orax .equ 6                    ;ORA
mne_peax .equ 2                    ;PEA
mne_peix .equ 33                   ;PEI
mne_perx .equ 60                   ;PER
mne_phax .equ 3                    ;PHA
mne_phbx .equ 10                   ;PHB
mne_phdx .equ 26                   ;PHD
mne_phkx .equ 38                   ;PHK
mne_phpx .equ 51                   ;PHP
mne_phxx .equ 75                   ;PHX
mne_phyx .equ 85                   ;PHY
mne_plax .equ 4                    ;PLA
mne_plbx .equ 11                   ;PLB
mne_pldx .equ 28                   ;PLD
mne_plpx .equ 52                   ;PLP
mne_plxx .equ 76                   ;PLX
mne_plyx .equ 86                   ;PLY
mne_repx .equ 49                   ;REP
mne_rolx .equ 41                   ;ROL
mne_rorx .equ 62                   ;ROR
mne_rtix .equ 37                   ;RTI
mne_rtlx .equ 46                   ;RTL
mne_rtsx .equ 67                   ;RTS
mne_sbcx .equ 14                   ;SBC
mne_secx .equ 19                   ;SEC
mne_sedx .equ 25                   ;SED
mne_seix .equ 34                   ;SEI
mne_sepx .equ 50                   ;SEP
mne_stax .equ 7                    ;STA
mne_stpx .equ 57                   ;STP
mne_stxx .equ 80                   ;STX
mne_styx .equ 89                   ;STY
mne_stzx .equ 91                   ;STZ
mne_taxx .equ 72                   ;TAX
mne_tayx .equ 82                   ;TAY
mne_tcdx .equ 24                   ;TCD
mne_tcsx .equ 66                   ;TCS
mne_tdcx .equ 17                   ;TDC
mne_trbx .equ 12                   ;TRB
mne_tsbx .equ 13                   ;TSB
mne_tscx .equ 22                   ;TSC
mne_tsxx .equ 79                   ;TSX
mne_txax .equ 8                    ;TXA
mne_txsx .equ 69                   ;TXS
mne_txyx .equ 90                   ;TXY
mne_tyax .equ 9                    ;TYA
mne_tyxx .equ 81                   ;TYX
mne_waix .equ 32                   ;WAI
mne_wdmx .equ 47                   ;WDM
mne_xbax .equ 0                    ;XBA
mne_xcex .equ 30                   ;XCE
;
;================================================================================
;
;MISCELLANEOUS CONSTANTS
;
halftab  .equ 4                    ;1/2 tabulation spacing
memprfx  .equ '>'                  ;memory dump prefix
memsepch .equ ':'                  ;memory dump separator
memsubch .equ '.'                  ;memory dump non-print char
srinit   .equ %00110000            ;SR initialization value
;
;================================================================================
;
;DIRECT PAGE STORAGE
;
reg_pbx  .equ zeropage             ;PB
reg_pcx  .equ reg_pbx+s_mpupbx     ;PC
reg_srx  .equ reg_pcx+s_mpupcx     ;SR
reg_ax   .equ reg_srx+s_mpusrx     ;.C
reg_xx   .equ reg_ax+s_word        ;.X
reg_yx   .equ reg_xx+s_word        ;.Y
reg_spx  .equ reg_yx+s_word        ;SP
reg_dpx  .equ reg_spx+s_mpuspx     ;DP
reg_dbx  .equ reg_dpx+s_mpudpx     ;DB
;
;
;	general workspace...
;
addra    .equ reg_dbx+s_mpudbx     ;address #1
addrb    .equ addra+s_addr         ;address #2
faca     .equ addrb+s_addr         ;primary accumulator
facax    .equ faca+s_pfac          ;extended primary accumulator
facb     .equ facax+s_pfac         ;secondary accumulator
facc     .equ facb+s_sfac          ;tertiary accumulator
operand  .equ facc+s_sfac          ;instruction operand
auxbufix .equ operand+s_oper       ;auxiliary buffer index
ibufidx  .equ auxbufix+s_byte      ;input buffer index
bitsdig  .equ ibufidx+s_byte       ;bits per numeral
numeral  .equ bitsdig+s_byte       ;numeral buffer
radix    .equ numeral+s_byte       ;radix index
admodidx .equ radix+s_byte         ;addressing mode index
charcnt  .equ admodidx+s_byte      ;character counter
instsize .equ charcnt+s_word       ;instruction size
mnepck   .equ instsize+s_word      ;encoded mnemonic
opcode   .equ mnepck+s_mnepck      ;current opcode
status   .equ opcode+s_byte        ;I/O status flag
xrtemp   .equ status+s_byte        ;temp .X storage
eopsize  .equ xrtemp+s_byte        ;entered operand size
flimflag .equ eopsize+s_byte       ;forced long immediate...
vecbrkia .equ flimflag+s_byte      ;system indirect BRK vector
;
;	xx000000
;	||
;	|+---------> 0: .X/.Y .equ  8 bits
;	|            1: .X/.Y .equ  18 bits
;	+----------> 0: .A .equ  8 bits
;	             1: .A .equ  16 bits
;
;	------------------------------------------------------------------------
;	During assembly, FLIMFLAG indicates the operand size used with an immed-
;	iate mode instruction, thus causing the following disassembly to display
;	the assembled  operand size.   During disassembly,  FLIMFLAG will mirror
;	the effect of the most recent REP or SEP instruction.
;	------------------------------------------------------------------------
;
iopsize  .equ flimflag+s_byte      ;operand size
range    .equ iopsize+s_byte       ;allowable radix range
vopsflag .equ range+s_byte         ;VOPS & ROPS mode bits
;
;
;	copy/fill workspace (overlaps some of the above)...
;
mcftwork .equ faca                 ;start of copy/fill code
mcftopc  .equ mcftwork+s_byte      ;instruction opcode
mcftbnk  .equ mcftopc+s_byte       ;banks
;
;================================================================================
;
;SUPERMON 816 JUMP TABLE
;
         *=_origin_
;
JMON     bra mon               ;cold start entry
JMONBRK  bra monbrk            ;software interrupt intercept
;
;
;================================================================================
;
;mon: SUPERMON 816 COLD START
;
mon

		     	REP #$10 		; 16 bit Index registers
	    	  LONGI ON
        	SEP #$20 		; 8 bit Accumulator
		      LONGA OFF
	    	  LDY   #$0000		; LOAD $00 INTO Y
OUTSTRLP:
        	LDA ALIVEM,Y   		; LOAD NEXT CHAR FROM STRING INTO ACC
        	CMP #$00		; IS NULL?
        	BEQ ENDOUTSTR		; YES, END PRINT OUT
        	JSR putcha  		; PRINT CHAR IN ACC
        	INY      		; Y=Y+1 (BUMP INDEX)
        	JMP OUTSTRLP		; DO NEXT CHAR
ENDOUTSTR:
          SEP #$10 		; 8 bit Index registers
		      LONGI OFF


          slonga
         lda vecbrki           ;BRK vector
         cmpw monbrk           ;pointing at monitor?
         bne moncontinue
         jmp monreg 		;yes, ignore cold start
;
moncontinue:
         sta vecbrkia          ;save vector for exit
         ldaw monbrk           ;Supermon 816 intercepts...
         sta vecbrki           ;BRK handler
         shortr                ;8 bit registers
         ldx #vopsflag-reg_pbx
;
_0000010 stz reg_pbx,x         ;clear DP storage
         dex
         bpl _0000010
;
;
;	initialize register shadows...
;
         lda #srinit
         sta reg_srx           ;status register
         slonga                 ;16 bit .A
         ldaw hwstack          ;top of hardware stack
         tcs                   ;set SP
         tdc                   ;get & save...
         sta reg_dpx           ;DP register
         ldaw 0
         shorta
         phk
         pla                   ;capture PB &...
         sta reg_pbx           ;set
         phb
         pla                   ;capture DB &...
         sta reg_dbx           ;set
;
;
;	print startup banner...
;
         pea mm_entry          ;"...ready..."
         bra moncom
;
;================================================================================
;
;monbrk: SOFTWARE INTERRUPT INTERCEPT
;
;	------------------------------------------------------------------------
;	This is the entry point taken when a BRK instruction is executed.  It is
;	assumed that the BRK  handler has pushed the registers to the stack that
;	are not automatically pushed by the MPU in response to BRK.
;	------------------------------------------------------------------------
;
monbrk
       	CLD			; VERIFY DECIMAL MODE IS OFF
	      CLC 			;
	      XCE 			; SET NATIVE MODE
        phb                     ;save DB
        phd                     ;save DP
        slonga                  ;16 bit .A
        pha
        ldaw $0000              ;set DPR
        tcd                     ;
        pla
        longr                 	;store 16 bit registers
        sta <reg_ax            	;.A
        stx <reg_xx            	;.X
        sty <reg_yx            	;.Y
        pla                   	;get DP &...
        sta <reg_dpx           	;store
        shortx
        plx                   	;get DB &...
        stx <reg_dbx           	;store
        plx                   	;get SR &...
        stx <reg_srx           	;store
        pla                   	;get PC &...
        sta <reg_pcx           	;store
        plx                   	;get PB &...
        stx <reg_pbx           	;store
        slonga
        ldaw hwstack            ;top of hardware stack
        tcs                     ;set SPR
       	cli                   	;reenable IRQs
        shorta
        lda #$00                ;set DBR
        pha
        PLB
        pea mm_brk              ;"*BRK"
;
;================================================================================
;
;moncom: COMMON ENTRY POINT
;
;	--------------------------------------
;	DO NOT directly call this entry point!
;	--------------------------------------
;
moncom   jsr sprint            ;print heading
         slonga
         tsc                   ;get SP &...
         sta <reg_spx           ;store
         rep #%11111111         ;clear SR &...
         sep #srinit            ;set default state
         sec                   ;see next
;
;================================================================================
;
;monreg: DISPLAY MPU REGISTERS
;
;	---------
;	syntax: R
;	---------
;
monreg   bcs _0010010          ;okay to proceed
;
         jmp monerr            ;error if called with a parm
;
_0010010 pea mm_regs
         jsr sprint            ;display heading
;
;
;	display program bank & counter...
;
         shorta
         lda <reg_pbx           ;PB
         jsr dpyhex            ;display as hex ASCII
         jsr printspc          ;inter-field space

         slonga
         lda <reg_pcx
         shorta
         jsr dpyhexw           ;display PC
         ldx #2
         jsr multspc           ;inter-field spacing
;
;
;	display SR in bitwise fashion...
;
         ldx <reg_srx           ;SR
         ldy #s_bibyte         ;bits in a byte
;
_0010020 txa                   ;remaining SR bits
         asl                   ;grab one of them
         tax                   ;save remainder
         lda #'0'              ;a clear bit but...
         adc #0                ;adjust if set &...
         jsr putcha            ;print
         dey                   ;bit processed
         bne _0010020          ;do another
;
;
;	display .C, .X, .Y, SP & DP...
;
_0010030 jsr printspc          ;spacing
         slonga
         lda reg_ax,y          ;get register value
         shorta
         jsr dpyhexw           ;convert & display

;         .rept s_word
           iny
           iny
;         .endr

         cpy #reg_dbx-reg_ax-2
         bcc _0010030          ;next

         pea mm_regs1
         jsr sprint            ;display heading
         slonga
         lda <reg_dpx          ;get register value
         shorta
         jsr dpyhexw           ;convert & display
;
;
;	display DB...
;
         jsr printspc          ;more spacing
         lda <reg_dbx           ;get DB &...
         jsr dpyhex            ;display it
;
;================================================================================
;
;monce: COMMAND EXECUTIVE
;
monce    shorta
         lda #0                ;default buffer index
;
moncea   shortr                ;alternate entry point
         sta ibufidx           ;(re)set buffer index
         pea mm_prmpt
         jsr sprint            ;display input prompt
         jsr input             ;await some input
;
_0020010 jsr getcharc          ;read from buffer
         beq monce             ;terminator, just loop
;
         cmp #a_blank
         beq _0020010          ;strip leading blanks
;
         ldx #n_mpctab-1       ;number of primary commands
;
_0020020 cmp mpctab,x          ;search primary command list
         bne _0020030
;
         txa                   ;get index
         asl                   ;double for offset
         tax
         slonga
         lda mpcextab,x        ;command address -1
         pha                   ;prime the stack
         shorta
         jmp getparm           ;evaluate parm & execute command
;
_0020030 dex
         bpl _0020020          ;continue searching primary commands
;
         ldx #n_radix-1        ;number of radices
;
_0020040 cmp radxtab,x         ;search conversion command list
         bne _0020050
;
         jmp monenv            ;convert & display parameter
;
_0020050 dex
         bpl _0020040
;
;================================================================================
;
;monerr: COMMON ERROR HANDLER
;
monerr   shortr                ;8 bit registers
;
monerraa jsr dpyerr            ;indicate an error &...
         bra monce             ;return to input loop

;
;================================================================================
;
;monasc: ASSEMBLE CODE
;
;	-----------------------------------------------------------------------
;	syntax: A <addr> <mnemonic> [<argument>]
;
;	After a line of code has been successfully assembled it will be disass-
;	embled & displayed,  & the monitor will prompt with the next address to
;	which code may be assembled.
;	-----------------------------------------------------------------------
;
monasc   bcc _0030020          ;assembly address entered
;
_0030010 jmp monerr            ;terminate w/error
;
;
;	evaluate assembly address...
;
_0030020 jsr facasize          ;check address...
         cmp #s_dword          ;range
         bcs _0030010          ;out of range - error
;
         jsr facaddra          ;store assembly address
;
;
;	initialize workspace...
;
         ldx #s_auxbuf-s_byte
;
_0030030 stz auxbuf,x          ;clear addressing mode buffer
         dex
         bne _0030030
;
         lda #a_blank
         sta auxbuf            ;preamble placeholder
         jsr clroper           ;clear operand
         stz auxbufix          ;reset addressing mode index
         stz flimflag          ;clear forced long immediate
         stz mnepck            ;clear encoded...
         stz mnepck+s_byte     ;mnemonic workspace
         stz vopsflag          ;clear 8/16 or relative flag
;
;
;	encode mnemonic...
;
         ldy #s_mnemon         ;expected mnemonic size
;
_0030040 jsr getcharw          ;get from buffer wo/whitespace
         bne _0030060          ;gotten
;
         cpy #s_mnemon         ;any input at all?
         bcc _0030050          ;yes
;
         jmp monce             ;no, abort further assembly
;
_0030050 jmp monasc10          ;incomplete mnemonic - error
;
_0030060 sec
         sbc #a_mnecvt         ;ASCII to binary factor
         ldx #n_shfenc         ;shifts required to encode
;
_0030070 lsr                   ;shift out a bit...
         ror mnepck+s_byte     ;into...
         ror mnepck            ;encoded mnemonic
         dex
         bne _0030070          ;next bit
;
         dey
         bne _0030040          ;get next char
;
;
;	test for copy instruction...
;	------------------------------------------------------------------------
;	The MVN & MVP instructions accept two operands & hence have an irregular
;	syntax.  Therefore, special handling is necessary to assemble either of
;	these instructions.
;
;	The official WDC syntax has the programmer entering a pair of 24 bit ad-
;	dresses as operands, with the assembler isolating bits 16-23 to	use as
;	operands.  This formality has been dispensed with in this monitor & the
;	operands are expected to be 8 bit bank values.
;	------------------------------------------------------------------------
;
         slonga                 ;16 bit load
         lda mnepck            ;packed menmonic
         ldx #opc_mvn          ;MVN opcode
         cmpw mne_mvn          ;is it MVN?
         beq monasc01          ;yes
;
         ldx #opc_mvp          ;MVP opcode
         cmpw mne_mvp          ;is it MVP?
         bne monasc02          ;no
;
;
;	assemble copy instruction...
;
monasc01 stx opcode            ;store relevant opcode
         shorta
         jsr instdata          ;get instruction data
         stx eopsize           ;effective operand size
         inx
         stx instsize          ;instruction size
         ldx #s_oper-s_word    ;operand index
         stx xrtemp            ;set it
;
_0040010 jsr ascbin            ;evaluate bank number
         bcs monasc04          ;conversion error
;
         beq monasc04          ;nothing returned - error
;
         jsr facasize          ;bank must be...
         cmp #s_word           ;8 bits
         bcs monasc04          ;it isn't - error
;
         lda faca              ;bank
         ldx xrtemp            ;operand index
         sta operand,x         ;store
         dec xrtemp            ;index=index-1
         bpl _0040010          ;get destination bank
;
         jsr getcharr          ;should be no more input
         bne monasc04          ;there is - error
;
         jmp monasc08          ;finish MVN/MVP assembly
;
;
;	continue with normal assembly...
;
monasc02 shorta                ;back to 8 bits
;
monasc03 jsr getcharw          ;get next char
         beq monasc06          ;EOI, no argument
;
         cmp #amp_flim
         bne _0050010          ;no forced long immediate
;
         lda flimflag          ;FLIM already set?
         bne monasc04          ;yes - error
;
         lda #flimmask
         sta flimflag          ;set flag &...
         bra monasc03          ;get next char
;
_0050010 cmp #amp_imm          ;immediate mode?
         beq _0050020          ;yes
;
         cmp #amp_ind          ;indirect mode?
         beq _0050020          ;yes
;
         cmp #amp_indl         ;indirect long mode?
         bne _0050030          ;no
;
_0050020 sta auxbuf            ;set addressing mode preamble
         inc auxbufix          ;bump aux buffer index &...
         bra _0050040          ;evaluate operand
;
_0050030 dec ibufidx           ;position back to char
;
_0050040 jsr ascbin            ;evaluate operand
         bne monasc05          ;evaluated
;
         bcs monasc04          ;conversion error
;
         lda auxbufix          ;no operand...any preamble?
         beq monasc06          ;no, syntax is okay so far
;
monasc04 jmp monasc10          ;abort w/error
;
monasc05 jsr facasize          ;size operand
         cmp #s_dword          ;max is 24 bits
         bcs monasc04          ;too big
;
         sta eopsize           ;save operand size
         jsr facaoper          ;store operand
;
monasc06 dec ibufidx           ;back to last char
         ldx auxbufix          ;mode buffer index
         bne _0060010          ;preamble in buffer
;
         inx                   ;step past preamble position
;
_0060010 jsr getcharc          ;get a char w/forced UC
         beq _0060030          ;EOI
;
         cpx #s_auxbuf         ;mode buffer full?
         bcs monasc04          ;yes, too much input
;
_0060020 sta auxbuf,x          ;store for comparison
         inx
         bne _0060010
;
;
;	evaluate mnemonic...
;
_0060030 ldx #n_mnemon-1       ;starting mnemonic index
;
monasc07 txa                   ;convert index...
         asl                   ;to offset
         tay                   ;now mnemonic table index
         slonga                 ;16 bit compare
         lda mnetab,y          ;get mnemonic from table
         cmp mnepck            ;compare to entered mnemonic
         shorta                ;back to 8 bits
         beq _0070020          ;match
;
_0070010 dex                   ;try next mnemonic
         bmi monasc04          ;unknown mnemonic - error
;
         bra monasc07          ;keep going
;
_0070020 stx mnepck            ;save mnemonic index
         txa
         ldx #0                ;trial opcode
;
_0070030 cmp mnetabix,x        ;search index table...
         beq _0070050          ;for a match
;
_0070040 inx                   ;keep going until we...
         bne _0070030          ;search entire table
;
         bra monasc04          ;this shouldn't happen!
;
;	---------------------------------------------------------------------
;	If the mnemonic index table search fails then there is a coding error
;	somewhere, as every entry in the mnemonic table is supposed to have a
;	matching cardinal index.
;	---------------------------------------------------------------------
;
;
;	evaluate addressing mode...
;
_0070050 stx opcode            ;save trial opcode
         jsr instdata          ;get related instruction data
         sta vopsflag          ;save 8/16 or relative flag
         stx iopsize           ;operand size
         inx
         stx instsize          ;instruction size
         ldx opcode            ;recover trial opcode
         tya                   ;addressing mode
         asl                   ;create table index
         tay
         slonga
         lda ms_lutab,y        ;mode lookup table
         sta addrb             ;set pointer
         shorta
         ldy #0
;
_0070060 lda (addrb),y         ;table addressing mode
         cmp auxbuf,y          ;entered addressing mode
         beq _0070080          ;okay so far
;
_0070070 lda mnepck            ;reload mnemonic index
         bra _0070040          ;wrong opcode for addresing mode
;
_0070080 ora #0                ;last char the terminator?
         beq _0070090          ;yes, evaluate operand
;
         iny
         bra _0070060          ;keep testing
;
;
;	evaluate operand...
;
_0070090 lda eopsize           ;entered operand size
         bne _0070100          ;non-zero
;
         ora iopsize           ;instruction operand size
         bne _0070070          ;wrong opcode - keep trying
;
         bra monasc08          ;assemble instruction
;
_0070100 bit vopsflag          ;is this a branch?
         bvs _0070160          ;yes, evaluate
;
         lda iopsize           ;instruction operand size
         bit vopsflag          ;variable size operand allowed?
         bmi _0070130          ;yes
;
         bit flimflag          ;was forced immediate set?
         bpl _0070110          ;no
;
         jmp monasc10          ;yes - error
;
_0070110 cmp eopsize           ;entered operand size
         bcc _0070070          ;operand too big
;
         sta eopsize           ;new operand size
         bra monasc08          ;assemble, otherwise...
;
_0070120 cmp eopsize           ;exact size match required
         bne _0070070          ;mismatch - wrong opcode
;
         bra monasc08          ;assemble
;
;
;	process variable size immediate mode operand...
;
_0070130 ldx eopsize           ;entered operand size
         cpx #s_xword          ;check size
         bcs monasc10          ;too big - error
;
         bit flimflag          ;forced long immediate?
         bpl _0070140          ;no
;
         ldx #s_word           ;promote operand size to...
         stx eopsize           ;16 bits
         bra _0070150
;
_0070140 cpx #s_word           ;16 bits?
         bne _0070150          ;no
;
         ldy #flimmask         ;yes so force long...
         sty flimflag          ;immediate disassembly
;
_0070150 ina                   ;new instruction operand size
         cmp eopsize           ;compare against operand size
         bcc _0070070          ;mismatch - can't assemble
;
         bra monasc08          ;okay, assemble
;
;
;	process relative branch...
;
_0070160 jsr targoff           ;compute branch offset
         bcs monasc10          ;branch out of range
;
         sta eopsize           ;effective operand size
;
;
;	assemble instruction...
;
monasc08 lda opcode            ;opcode
         stail addra           ;store at assembly address
         ldx eopsize           ;any operand to process?
         beq _0080020          ;no
;
         txy                   ;also storage offset
;
_0080010 dex
         lda operand,x         ;get operand byte &...
         staily addra          ;poke into memory
         dey
         bne _0080010          ;next
;
_0080020 lda #a_cr
         jsr putcha            ;return to left margin
         lda #asmprfx          ;assembly prefix
         jsr dpycodaa          ;disassemble & display
;
;
;	prompt for next instruction...
;
monasc09 lda #a_blank
         ldx #ascprmct-1
;
_0090010 sta ibuffer,x         ;prepare buffer for...
         dex                   ;next instruction
         bpl _0090010
;
         lda #asmprfx          ;assemble code...
         sta ibuffer           ;prompt prefix
         lda addra+s_word      ;next instruction address bank
         jsr binhex            ;convert to ASCII
         sta ibuffer+apadrbkh  ;store MSN in buffer
         stx ibuffer+apadrbkl  ;store LSN in buffer
         lda addra+s_byte      ;next instruction address MSB
         jsr binhex
         sta ibuffer+apadrmbh
         stx ibuffer+apadrmbl
         lda addra             ;next instruction address LSB
         jsr binhex
         sta ibuffer+apadrlbh
         stx ibuffer+apadrlbl
         lda #ascprmct         ;effective input count
         jmp moncea            ;reenter input loop
;
;
;	process assembly error...
;
monasc10 jsr dpyerr            ;indicate error &...
         bra monasc09          ;prompt w/same assembly address
;
;================================================================================
;
;mondsc: DISASSEMBLE CODE
;
;	-----------------------------
;	syntax: D [<addr1> [<addr2>]]
;	-----------------------------
;
mondsc   bcs _0100010          ;no parameters
;
         stz flimflag          ;reset to 8 bit mode
         jsr facasize          ;check starting...
         cmp #s_dword          ;address
         bcs _0100050          ;out of range - error
;
         jsr facaddra          ;copy starting address
         jsr getparm           ;get ending address
         bcc _0100020          ;gotten
;
_0100010 jsr clrfaca           ;clear accumulator
         slonga
         clc
         lda addra             ;starting address
         adcw n_dbytes         ;default bytes
         sta faca              ;effective ending address
         shorta
         lda addra+s_word      ;starting bank
         adc #0
         sta faca+s_word       ;effective ending bank
         bcs _0100050          ;end address > $FFFFFF
;
_0100020 jsr facasize          ;check ending...
         cmp #s_dword          ;address
         bcs _0100050          ;out of range - error
;
         jsr facaddrb          ;set ending address
         jsr getparm           ;check for excess input
         bcc _0100050          ;present - error
;
         jsr calccnt           ;calculate bytes
         bcc _0100050          ;end < start
;
_0100030 jsr teststop          ;test for display stop
         bcs _0100040          ;stopped
;
         jsr newline           ;next line
         jsr dpycod            ;disassemble & display
         jsr decdcnt           ;decrement byte count
         bcc _0100030          ;not done
;
_0100040 jmp monce             ;back to main loop
;
_0100050 jmp monerr            ;address range error
;
;================================================================================
;
;monjmp: EXECUTE CODE
;
;	-------------------------------------------------------------
;	syntax: G [<dp>]
;
;	If no address is specified, the current values in the PB & PC
;	shadow registers are used.
;	-------------------------------------------------------------
;
monjmp   jsr setxaddr          ;set execution address
         bcs monjmpab          ;out of range - error
;
         jsr getparm           ;check for excess input
         bcc monjmpab          ;too much input - error
;
         slonga                 ;16 bit .A
         lda reg_spx
         tcs                   ;restore SP
;
monjmpaa shorta
         lda reg_pbx
         pha                   ;restore PB
         slonga
         lda reg_pcx
         pha                   ;restore PC
         shorta
         lda reg_srx
         pha                   ;restore SR
         lda reg_dbx
         pha
         plb                   ;restore DB
         longr
         lda reg_dpx
         tcd                   ;restore DP
         lda reg_ax            ;restore .C
         ldx reg_xx            ;restore .X
         ldy reg_yx            ;restore .Y
         rti                   ;execute code
;
monjmpab jmp monerr            ;error
;
;================================================================================
;
;monjsr: EXECUTE CODE AS SUBROUTINE
;
;	------------------------------------------------------------
;	syntax: J [<dp>]
;
;	If no address is specified the current values in the PB & PC
;	shadow registers are used.   An RTS at the end of the called
;	subroutine will return control to the monitor  provided  the
;	stack remains in balance.
;	------------------------------------------------------------
;
monjsr   jsr setxaddr          ;set execution address
         bcs monjmpab          ;out of range - error
;
         jsr getparm           ;check for excess input
         bcc monjmpab          ;too much input - error
;
         slonga
         lda reg_spx
         tcs                   ;restore SP &...
         jsr monjmpaa          ;call subroutine
         php                   ;push SR
         longr
         sta reg_ax            ;save...
         stx reg_xx            ;register...
         sty reg_yx            ;returns
         shortx                ;8 bit .X & .Y
         plx                   ;get & save...
         stx reg_srx           ;return SR
         tsc                   ;get & save...
         sta reg_spx           ;return SP
         tdc                   ;get & save...
         sta reg_dpx           ;DP pointer
         shorta                ;8 bit .A
         phk                   ;get &...
         pla                   ;save...
         sta reg_pbx           ;return PB
         phb                   ;get &...
         pla                   ;save...
         sta reg_dbx           ;return DB
         pea mm_rts            ;"*RET"
         jmp moncom            ;return to monitor
;
;================================================================================
;
;monchm: CHANGE and/or DUMP MEMORY
;
;	--------------------------------------------
;	syntax: > [<addr> <operand> [<operand>]...]
;
;	> <addr> without operands will dump 16 bytes
;	of memory, starting at <addr>.
;	--------------------------------------------
;
monchm   bcs _0110030          ;no address given - quit
;
         jsr facasize          ;size address
         cmp #s_dword
         bcs _0110040          ;address out of range - error
;
         jsr facaddra          ;set starting address
         jsr getpat            ;evaluate change pattern
         bcc _0110010          ;entered
;
         bpl _0110020          ;not entered
;
         bra _0110040          ;evaluation error
;
_0110010 dey                   ;next byte
         bmi _0110020          ;done
;
         lda auxbuf,y          ;write pattern...
         staily addra          ;to memory
         bra _0110010          ;next
;
_0110020 jsr newline           ;next line
         jsr dpymem            ;regurgitate changes
;
_0110030 jmp monce             ;back to command loop
;
_0110040 jmp monerr            ;goto error handler
;
;================================================================================
;
;moncmp: COMPARE MEMORY
;
;	-----------------------------
;	syntax: C <start> <end> <ref>
;	-----------------------------
;
moncmp   bcs _0120030          ;start not given - quit
;
         jsr enddest           ;get end & reference addresses
         bcs _0120040          ;range or other error
;
         stz xrtemp            ;column counter
;
_0120010 jsr teststop          ;check for stop
         bcs _0120030          ;abort
;
         ldail addra           ;get from reference location
         cmpil operand         ;test against compare location
         beq _0120020          ;match, don't display address
;
         jsr dpycaddr          ;display current location
;
_0120020 jsr nxtaddra          ;next reference location
         bcs _0120030          ;done
;
         slonga
         inc operand           ;bump bits 0-15
         shorta
         bne _0120010
;
         inc operand+s_word    ;bump bits 16-23
         bra _0120010
;
_0120030 jmp monce             ;return to command exec
;
_0120040 jmp monerr            ;goto error handler
;
;================================================================================
;
;moncpy: COPY (transfer) MEMORY
;
;	--------------------------------
;	syntax: T <start> <end> <target>
;	--------------------------------
;
moncpy   bcs _0130040          ;start not given - quit
;
         jsr enddest           ;get end & target addresses
         bcs _0130050          ;range or other error
;
         slonga
         sec
         lda addrb             ;ending address
         sbc addra             ;starting address
         bcc _0130050          ;start > end - error
;
         sta facb              ;bytes to copy
         shorta
         longx
         lda operand+s_word    ;target bank
         ldy operand           ;target address
         cmp addra+s_word      ;source bank
         slonga
         bne _0130020          ;can use forward copy
;
         cpy addra             ;source address
         bcc _0130020          ;can use forward copy
;
         bne _0130010          ;must use reverse copy
;
         bra _0130050          ;copy in place - error
;
_0130010 lda facb              ;get bytes to copy
         pha                   ;protect
         jsr lodbnk            ;load banks
         jsr cprvsup           ;do reverse copy setup
         pla                   ;get bytes to copy
         tax                   ;save a copy
         clc
         adc operand           ;change target to...
         tay                   ;target end
         txa                   ;recover bytes to copy
         ldx addrb             ;source end
         bra _0130030
;
_0130020 lda facb              ;get bytes to copy
         pha                   ;protect
         jsr lodbnk            ;load banks
         jsr cpfwsup           ;do forward copy setup
         pla                   ;get bytes to copy
         ldx addra             ;source start
;
_0130030 jmp mcftwork          ;copy memory
;
_0130040 jmp monce             ;back to executive
;
_0130050 jmp monerr            ;error
;
;================================================================================
;
;mondmp: DISPLAY MEMORY RANGE
;
;	-----------------------------
;	syntax: M [<addr1> [<addr2>]]
;	-----------------------------
;
mondmp   bcs _0140010          ;no parameters
;
         jsr facasize          ;check address...
         cmp #s_dword          ;range
         bcs _0140050          ;address out of range
;
         jsr facaddra          ;copy starting address
         jsr getparm           ;get ending address
         bcc _0140020          ;gotten
;
_0140010 jsr clrfaca           ;clear accumulator
         slonga
         clc
         lda addra             ;starting address
         adcw n_mbytes         ;default bytes
         sta faca              ;effective ending address
         shorta
         lda addra+s_word      ;starting bank
         adc #0
         sta faca+s_word       ;effective ending bank
         bcs _0140050          ;end address > $FFFFFF
;
_0140020 jsr facasize          ;check ending address...
         cmp #s_dword          ;range
         bcs _0140050          ;out of range - error
;
         jsr facaddrb          ;copy ending address
         jsr getparm           ;check for excess input
         bcc _0140050          ;error
;
         jsr calccnt           ;calculate bytes to dump
         bcc _0140050          ;end < start
;
_0140030 jsr teststop          ;test for display stop
         bcs _0140040          ;stopped
;
         jsr newline           ;next line
         jsr dpymem            ;display
         jsr decdcnt           ;decrement byte count
         bcc _0140030          ;not done
;
_0140040 jmp monce             ;back to main loop
;
_0140050 jmp monerr            ;address range error
;
;================================================================================
;
;monfil: FILL MEMORY
;
;	-----------------------------------------
;	syntax: F <start> <end> <fill>
;
;	<start> & <end> must be in the same bank.
;	-----------------------------------------
;
monfil   bcs _0150010          ;start not given - quit
;
         jsr facasize          ;check size
         cmp #s_dword
         bcs _0150020          ;out of range - error...
;
         jsr facaddra          ;store start
         jsr getparm           ;evaluate end
         bcs _0150020          ;not entered - error
;
         jsr facasize          ;check size
         cmp #s_dword
         bcs _0150020          ;out of range - error
;
         lda faca+s_word       ;end bank
         cmp addra+s_word      ;start bank
         bne _0150020          ;not same - error
;
         jsr facaddrb          ;store <end>
         slonga
         sec
         lda addrb             ;ending address
         sbc addra             ;starting address
         bcc _0150020          ;start > end - error
;
         sta facb              ;bytes to copy
         shorta
         jsr getparm           ;evaluate <fill>
         bcs _0150020          ;not entered - error
;
         jsr facasize          ;<fill> should be...
         cmp #s_word           ;8 bits
         bcs _0150020          ;it isn't - error
;
         jsr facaoper          ;store <fill>
         jsr getparm           ;should be no more parameters
         bcc _0150020          ;there are - error
;
         lda operand           ;<fill>
         stail addra           ;fill 1st location
         longr                 ;16 bit operations
         lda facb              ;get byte count
         beq _0150010          ;only 1 location - finished
;
         dea                   ;zero align &...
         pha                   ;protect
         shorta
         lda addra+s_word      ;start bank
         xba
         lda addrb+s_word      ;end bank
         jsr cpfwsup           ;do forward copy setup
         pla                   ;recover fill count
         ldx addra             ;fill-from starting location
         txy
         iny                   ;fill-to starting location
         jmp mcftwork          ;fill memory
;
_0150010 jmp monce             ;goto command executive
;
_0150020 jmp monerr            ;goto error handler
;
;================================================================================
;
;monhnt: SEARCH (hunt) MEMORY
;
;	-----------------------------------
;	syntax: H <addr1> <addr2> <pattern>
;	-----------------------------------
;
monhnt   bcs _0160050          ;no start address
;
         jsr facasize          ;size starting address
         cmp #s_dword
         bcs _0160060          ;address out of range - error
;
         jsr facaddra          ;store starting address
         jsr getparm           ;evaluate ending address
         bcs _0160060          ;no address - error
;
         jsr facasize          ;size ending address
         cmp #s_dword
         bcs _0160060          ;address out of range - error
;
         jsr facaddrb          ;store ending address
         jsr calccnt           ;calculate byte range
         bcc _0160060          ;end < start
;
         jsr getpat            ;evaluate search pattern
         bcs _0160060          ;error
;
         stz xrtemp            ;clear column counter
;
_0160010 jsr teststop          ;check for stop
         bcs _0160050          ;abort
;
         ldy auxbufix          ;pattern index
;
_0160020 dey
         bmi _0160030          ;pattern match
;
         ldaily addra          ;get from memory
         cmp auxbuf,y          ;test against pattern
         bne _0160040          ;mismatch, next location
;
         beq _0160020          ;match, keep testing
;
_0160030 jsr dpycaddr          ;display current location
;
_0160040 jsr nxtaddra          ;next location
         bcc _0160010          ;not done
;
_0160050 jmp monce             ;back to executive
;
_0160060 jmp monerr            ;goto error handler
;
;================================================================================
;
;monenv: CONVERT NUMERIC VALUE
;
;	----------------------
;	syntax: <radix><value>
;	----------------------
;
monenv   jsr getparmr          ;reread & evaluate parameter
         bcs _0170020          ;none entered
;
         ldx #0                ;radix index
         ldy #n_radix          ;number of radices
;
_0170010 phy                   ;save counter
         phx                   ;save radix index
         jsr newline           ;next line &...
         jsr clearlin          ;clear it
         lda #a_blank
         ldx #halftab
         jsr multspc           ;indent 1/2 tab
         plx                   ;get radix index but...
         phx                   ;put it back
         lda radxtab,x         ;get radix
         jsr binasc            ;convert to ASCII
         phy                   ;string address MSB
         phx                   ;string address LSB
         jsr sprint            ;print
         plx                   ;get index again
         ply                   ;get counter
         inx
         dey                   ;all radices handled?
         bne _0170010          ;no

_0170020 jmp monce             ;back to command exec
;
;================================================================================
;
;monchr: CHANGE REGISTERS
;
;	------------------------------------------------------
;	syntax: ; [PB [PC [.S [.C [.X [.Y [SP [DP [DB]]]]]]]]]
;
;	; with no parameters is the same as the R command.
;	------------------------------------------------------
;
monchr   bcs _0570040          ;dump registers & quit
;
         ldy #0                ;register counter
         sty facc              ;initialize register index
;
_0570010 jsr facasize          ;get parameter size
         cmp rcvltab,y         ;check against size table
         bcs _0570050          ;out of range
;
         lda rcvltab,y         ;determine number of bytes...
         cmp #s_word+1         ;to store
         ror facc+s_byte       ;condition flag
         bpl _0570020          ;8 bit register size
;
         slonga                 ;16 bit register size
;
_0570020 ldx facc              ;get register index
         lda faca              ;get parm
         sta reg_pbx,x         ;put in shadow storage
         shorta
         asl facc+s_byte       ;mode flag to carry
         txa                   ;register index
         adc #s_byte           ;at least 1 byte stored
         sta facc              ;save new index
         jsr getparm           ;get a parameter
         bcs _0570040          ;EOI
;
         iny                   ;bump register count
         cpy #n_regchv         ;all registers processed?
         bne _0570010          ;no, keep going
;
_0570030 jsr alert             ;excessive input
;
_0570040 jmp monreg            ;display changes
;
_0570050 jmp monerr            ;goto error handler
;
;================================================================================
;
;monxit: EXIT TO OPERATING ENVIRONMENT
;
;	---------
;	syntax: X
;	---------
;
;monxit   bcc _0180020          ;no parameters allowed
;
;         slonga
;        lda vecbrki           ;BRK indirect vector
;         cmpw monbrk           ;we intercept it?
;         bne _0180010          ;no, don't change it
;
;         lda vecbrkia          ;old vector
;         sta vecbrki           ;restore it
;         stz vecbrkia          ;invalidate old vector
;
;_0180010 shortr
;         jml vecexit           ;long jump to exit
;
;_0180020 jmp monerr            ;goto error handler
;
; * * * * * * * * * * * * * * * * * * * * * * * *
; * * * * * * * * * * * * * * * * * * * * * * * *
; * *                                         * *
; * * S T A R T   o f   S U B R O U T I N E S * *
; * *                                         * *
; * * * * * * * * * * * * * * * * * * * * * * * *
; * * * * * * * * * * * * * * * * * * * * * * * *
;
;dpycaddr: DISPLAY CURRENT ADDRESS IN COLUMNS
;
dpycaddr ldx xrtemp            ;column count
         bne _0190010          ;not at right side
;
         jsr newline           ;next row
         ldx #n_hccols         ;max columns
;
_0190010 cpx #n_hccols         ;max columns
         beq _0190020          ;at left margin
;
         lda #a_ht
         jsr putcha            ;tab a column
;
_0190020 dex                   ;one less column
         stx xrtemp            ;save column counter
         jmp prntladr          ;print reference address
;
;================================================================================
;
;dpycod: DISASSEMBLE & DISPLAY CODE
;
;	------------------------------------------------------------------------
;	This function disassembles & displays the machine code at  the  location
;	pointed to by ADDRA.  Upon return, ADDRA will point to the opcode of the
;	next instruction.   The entry point at DPYCODAA  should be called with a
;	disassembly prefix character loaded in .A.   If entered  at  DPYCOD, the
;	default character will be display at the beginning of each  disassembled
;	instruction.
;
;	The disassembly of immediate mode instructions that can take an 8 or  16
;	bit operand is affected by the bit pattern that is  stored  in  FLIMFLAG
;	upon entry to this function:
;
;	    FLIMFLAG: xx000000
;	              ||
;	              |+---------> 0:  8 bit .X or .Y operand
;	              |            1: 16 bit .X or .Y operand
;	              +----------> 0:  8 bit .A or BIT # operand
;	                           1: 16 bit .A or BIT # operand
;
;	FLIMFLAG is conditioned according to the operand of  the  most  recently
;	disassembled REP or SEP instruction.   Hence repetitive  calls  to  this
;	subroutine will usually result in the correct disassembly of 16 bit imm-
;	ediate mode instructions.
;	------------------------------------------------------------------------
;
dpycod   lda #disprfx          ;default prefix
;
;
;	alternate prefix display entry point...
;
dpycodaa jsr putcha            ;print prefix
         jsr printspc          ;space
         jsr prntladr          ;print long address
         jsr printspc          ;space to opcode field
         jsr getbyte           ;get opcode
         sta opcode            ;save &...
         jsr printbyt          ;display as hex
;
;
;	decode menmonic & addressing info...
;
         ldx opcode            ;current mnemonic
         lda mnetabix,x        ;get mnemonic index
         asl                   ;double for...
         tay                   ;mnemonic table offset
         slonga                 ;16 bit load
         lda mnetab,y          ;copy encoded mnemonic to...
         sta mnepck            ;working storage
         shorta                ;back to 8 bits
         jsr instdata          ;extract mode & size data
         sta vopsflag          ;save mode flags
         sty admodidx          ;save mode index
         asl                   ;variable immediate instruction?
         bcc dpycod01          ;no, effective operand size in .X
;
;
;	determine immediate mode operand size...
;
         lda opcode            ;current opcode
         bit flimflag          ;operand display mode
         bpl _0200010          ;8 bit .A & BIT immediate mode
;
         and #aimmaska         ;determine if...
         cmp #aimmaskb         ;.A or BIT immediate
         beq _0200030          ;display 16 bit operand
;
         lda opcode            ;not .A or BIT immediate
;
_0200010 bvc dpycod01          ;8 bit .X/.Y immediate mode
;
         ldy #n_vopidx-1       ;opcodes to test
;
_0200020 cmp vopidx,y          ;looking for LDX #, CPY #, etc.
         beq _0200040          ;disassemble a 16 bit operand
;
         dey
         bpl _0200020          ;keep trying
;
         bra dpycod01          ;not .X or .Y immediate
;
_0200030 lda opcode            ;reload
;
_0200040 inx                   ;16 bit operand
;
;
;	get & display operand bytes...
;
dpycod01 stx iopsize           ;operand size...
         inx                   ;plus opcode becomes...
         stx instsize          ;instruction size
         stx charcnt           ;total bytes to process
         lda #n_opcols+2       ;total operand columns plus WS
         sta xrtemp            ;initialize counter
         jsr clroper           ;clear operand
         ldy iopsize           ;operand size
         beq _0210020          ;no operand
;
         ldx #0                ;operand index
;
_0210010 jsr getbyte           ;get operand byte
         sta operand,x         ;save
         phx                   ;protect operand index
         jsr printbyt          ;print operand byte
         dec xrtemp            ;3 columns used, 2 for...
         dec xrtemp            ;operand nybbles &...
         dec xrtemp            ;1 for whitespace
         plx                   ;get operand index
         inx                   ;bump it
         dey
         bne _0210010          ;next
;
_0210020 ldx xrtemp            ;operand columns remaining
         jsr multspc           ;space to mnemonic field
;
;
;	display mnemonic...
;
         ldy #s_mnemon         ;size of ASCII mnemonic
;
_0210030 lda #0                ;initialize char
         ldx #n_shfenc         ;shifts to execute
;
_0210040 asl mnepck            ;shift encoded mnemonic
         rol mnepck+s_byte
         rol
         dex
         bne _0210040
;
         adc #a_mnecvt         ;convert to ASCII &...
         pha                   ;stash
         dey
         bne _0210030          ;continue with mnemonic
;
         ldy #s_mnemon
;
_0210050 pla                   ;get mnenmonic byte
         jsr putcha            ;print it
         dey
         bne _0210050
;
;
;	display operand...
;
         lda iopsize           ;operand size
         beq clearlin          ;zero, disassembly finished
;
         jsr printspc          ;space to operand field
         bit vopsflag          ;check mode flags
         bvc dpycod02          ;not a branch
;
         jsr offtarg           ;compute branch target
         ldx instsize          ;effective instruction size
         dex
         stx iopsize           ;effective operand size
;
dpycod02 stz vopsflag          ;clear
         lda admodidx          ;instruction addressing mode
         cmp #am_move          ;block move instruction?
         bne _0220010          ;no
;
         ror vopsflag          ;yes
;
_0220010 asl                   ;convert addressing mode to...
         tax                   ;symbology table index
         slonga                 ;do a 16 bit load
         lda ms_lutab,x        ;addressing symbol pointer
         pha
         shorta                ;back to 8 bit loads
         ldy #0
         ldasi 1               ;get 1st char
         cmp #a_blank
         beq _0220020          ;no addresing mode preamble
;
         jsr putcha            ;print preamble
;
_0220020 lda #c_hex
         jsr putcha            ;operand displayed as hex
         ldy iopsize           ;operand size = index
;
_0220030 dey
         bmi _0220040          ;done with operand
;
         lda operand,y         ;get operand byte
         jsr dpyhex            ;print operand byte
         bit vopsflag          ;block move?
         bpl _0220030          ;no
;
         stz vopsflag          ;reset
         phy                   ;protect operand index
         pea ms_move
         jsr sprint            ;display MVN/MVP operand separator
         ply                   ;recover operand index again
         bra _0220030          ;continue
;
_0220040 plx                   ;symbology LSB
         ply                   ;symbology MSB
         inx                   ;move past preamble
         bne _0220050
;
         iny
;
_0220050 phy
         phx
         jsr sprint            ;print postamble, if any
;
;
;	condition immediate mode display format...
;
dpycod03 lda operand           ;operand LSB
         and #pfmxmask         ;isolate M & X bits
         asl                   ;shift to match...
         asl                   ;FLIMFLAG alignment
         ldx opcode            ;current instruction
         cpx #opc_rep          ;was it REP?
         bne _0230010          ;no
;
         tsb flimflag          ;set flag bits as required
         bra clearlin
;
_0230010 cpx #opc_sep          ;was it SEP?
         bne clearlin          ;no, just exit
;
         trb flimflag          ;clear flag bits as required
;
;================================================================================
;
;clearlin: CLEAR DISPLAY LINE
;
clearlin
	rts
;
;================================================================================
;
;dpyibuf: DISPLAY MONITOR INPUT BUFFER CONTENTS
;
dpyibuf  pea ibuffer
         bra dpyerraa
;
;================================================================================
;
;dpymem: DISPLAY MEMORY
;
;	------------------------------------------------------------
;	This function displays 16 bytes of memory as hex values & as
;	ASCII equivalents.  The starting address for the display is
;	in ADDRA & is expected to be a 24 bit address.  Upon return,
;	ADDRA will point to the start of the next 16 bytes.
;	------------------------------------------------------------
;
dpymem   shortr
         stz charcnt           ;reset
;         lda #memprfx
;         jsr putcha            ;display prefix
         jsr prntladr          ;print 24 bit address
         ldx #0                ;string buffer index
         ldy #n_dump           ;bytes per line
;
_0240010 jsr getbyte           ;get from RAM, also...
         pha                   ;save for decoding
         phx                   ;save string index
         jsr printbyt          ;display as hex ASCII
         inc charcnt           ;bytes displayed +1
         plx                   ;recover string index &...
         pla                   ;byte
         cmp #a_blank          ;printable?
         bcc _0240020          ;no
;
         cmp #a_del
         bcc _0240030          ;is printable
;
_0240020 lda #memsubch         ;substitute character
;
_0240030 sta ibuffer,x         ;save char
         inx                   ;bump index
         dey                   ;byte count -= 1
         bne _0240010          ;not done
;
         stz ibuffer,x         ;terminate ASCII string
         lda #memsepch
         jsr putcha            ;separate ASCII from bytes
         jsr dpyibuf           ;display ASCII equivalents
         rts
;
;================================================================================
;
;dpyerr: DISPLAY ERROR SIGNAL
;
dpyerr   pea mm_err            ;"*ERR"
;
dpyerraa jsr sprint
         rts
;
;================================================================================
;
;gendbs: GENERATE DESTRUCTIVE BACKSPACE
;
gendbs   pea dc_bs             ;destructive backspace
         bra dpyerraa
;
;================================================================================
;
;prntladr: PRINT 24 BIT CURRENT ADDRESS
;
prntladr php                   ;protect register sizes
         shorta
         lda addra+s_word      ;get bank byte &...
         jsr dpyhex            ;display it
         slonga
         lda addra             ;get 16 bit address
         plp                   ;restore register sizes
;
;================================================================================
;
;dpyhexw: DISPLAY BINARY WORD AS HEX ASCII
;
;	------------------------------------
;	Preparatory Ops: .C: word to display
;
;	Returned Values: .C: used
;	                 .X: used
;	                 .Y: entry value
;	------------------------------------
;
dpyhexw  php                   ;save register sizes
         slonga
         pha                   ;protect value
         shorta
         xba                   ;get MSB &...
         jsr dpyhex            ;display
         slonga
         pla                   ;recover value
         shorta                ;only LSB visible
         plp                   ;reset register sizes
;
;================================================================================
;
;dpyhex: DISPLAY BINARY BYTE AS HEX ASCII
;
;	------------------------------------
;	Preparatory Ops: .A: byte to display
;
;	Returned Values: .A: used
;	                 .X: used
;	                 .Y: entry value
;	------------------------------------
;
dpyhex   jsr binhex            ;convert to hex ASCII
         jsr putcha            ;print MSN
         txa
         jmp putcha            ;print LSN
;
;================================================================================
;
;multspc: PRINT MULTIPLE BLANKS
;
;	------------------------------------------------
;	Preparatory Ops : .X: number of blanks to print
;
;	Register Returns: none
;
;	Calling Example : ldx #3
;	                  jsr multspc    ;print 3 spaces
;
;	Notes: This sub will print 1 blank if .X=0.
;	------------------------------------------------
;

multspc  txa
         bne _0250010          ;blank count specified
;
         inx                   ;default to 1 blank
;
_0250010 jsr printspc
         dex
         bne _0250010
;
         rts
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
